drhalftone/AuV2-SLI/LauPythonCamera_Pt_Stack/mech/README.md

# Mechanical models — camera sensor, bracket, stack shroud, and the printed enclosure

| | writes | |
|---|---|---|
| `gen_sensor_step.py` | `../3dmodels/NOIP1SN1300A_LCC48.step` | the PYTHON 1300 package — the reference body everything else is designed around |
| `gen_socket_tile.py` | `../3dmodels/camera_socket_tile.step` | iteration 0 of the bracket: the contact tile |
| `gen_stack_shroud.py` | `../3dmodels/stack_shroud_<layer>.step` | **CNC aluminium** shroud rings, one per board of the Alchitry stack |
| `gen_lens_box.py` | `../3dmodels/camera_lens_box.step` | **C-mount lens box** — open-bottomed, straddles the board, gravity-seated lens. Also the **upper half** of the two-part enclosure |
| `gen_base_box.py` | `../3dmodels/camera_base_box.step` | **base box** — the lower half: encloses the Hd+/Ft+/Pt V2 and sandwiches to the lens box |
| `gen_enclosure_assembly.py` | `../3dmodels/camera_enclosure_assembly.step` | **both halves in one file** — what you open to check they meet; not a printed part |
| `gen_stack_assembly.py` | `../3dmodels/stack/*.step` | **the real boards**: camera + ESP32 card exported from KiCad, Pt V2 / Ft+ / Hd from Alchitry's STEPs, mated on the DF40 sites into `board_stack.step`, and with both case halves into `camera_stack_enclosure.step`. Needs OCP (cadquery) and kicad-cli; not a printed part |
| `gen_lens_holder.py` | `../3dmodels/camera_lens_holder.step` | M12 / S-mount alternative: plate on four posts with a threaded barrel |
| `step_writer.py` | — | shared AP214 writer and 2D helpers |
| `check_step.py` | — | validates any of the above |

Regenerate; do not hand-edit a STEP. Output is byte-reproducible, so a regenerated file
that differs is a real change.

```
python gen_sensor_step.py                    # typical dimensions
python gen_sensor_step.py --tolerance max    # worst-case envelope
python gen_socket_tile.py
python gen_lens_box.py --bosses --open-face W --pcb-t 7.1 --washer-t 2.5 --port-notch W:2.5:20.5:-0.5:2.5 --port-notch W:-8.0:7.0:-5.0:1.0   # spacer stack (d6201f5) + USB-C notches
python gen_base_box.py --open-face W         # ...and the lower half: 24.5 mm spacer stack, nut raised for M2 x 30
python gen_enclosure_assembly.py             # both halves in ONE file, to check the fit
python gen_stack_assembly.py                 # real board stack (camera/Pt/Ft+/ESP32/Hd) + both halves, ~1.5 min
python gen_lens_holder.py                    # the M12 alternative
python check_step.py
```

The **printed enclosure is those two commands** — `gen_lens_box.py` is the upper half and
`gen_base_box.py` the lower, split on the lens box skirt bottom at z = −7.10 (spacer stack). Run them in
that order: the base box reads the lens box's STEP and refuses to emit if the halves would not
meet. See [the base box](#gen_base_boxpy--the-base-box-and-the-two-part-enclosure) at the end.

The first section below covers the sensor; [the socket tile](#the-socket-tile-iteration-0)
and [the lens mounts](#the-lens-mounts) are further down.

## The lens mounts

Both read `../LauPythonCamera_Pt_Stack.kicad_pcb` on **every run** for the board outline,
the four Ø2.2 corner holes, U1's position and rotation, and every component courtyard.
Neither hard-codes board geometry, and both **fail the build** rather than warn when a
wall, post or boss would land on a part. A holder that fouls a 0402 is something you
discover with a scalpel.

The optical axis is **not** the package centre. `OPTICAL_CENTER = (-0.17924, +1.36714)`
(Table 32) puts it at KiCad **(135.821, 80.633)** with U1 at (136, 82) unrotated. Skipping
that offset decentres the image and looks perfectly plausible while doing so.

### `gen_lens_box.py` — C-mount (preferred)

An open-bottomed box. The lens is not threaded into anything: its flange shoulder rests on
the top face and gravity holds it, board flat on a table. The bore is a **thread-in** hole,
25.4 − 0.1 = **25.3 mm** (`--bore-clear -0.10`): the lens screws into the plastic and cuts its
own thread until the shoulder lands on the top face. The number came off a printed test plate
(`gen_bore_test_plate.py`, ten holes 26.0 → 24.2 mm): 25.2 threads, 25.3 is the better fit.
`--bore-clear 0.80` restores the old 26.2 mm clearance hole.

**USB-C cable notches** (`--port-notch`) are cut up from the bottom of the **west** skirt, where the stack's USB-C ports face. Positions come from Alchitry's own STEP models, placed by `gen_stack_assembly.py`:

| port | receptacle (y, z) | notch | why |
|---|---|---|---|
| Pt V2 `J2` | y 6.97..16.03, z -6.59..-2.32 | `W:2.5:20.5:-0.5:2.5` -- 18 wide, to z -0.5, R2.5 | the port is entirely behind the skirt; a 12.4 x 6.6 overmold needs y 5.3..17.7, z -7.8..-1.2 |
| Ft+ `X1` | y -4.97..3.97, z -12.50..-8.40 | `W:-8.0:7.0:-5.0:1.0` -- 15 wide, 2.1 tall, R1.0 | the base box is open here, but an overmold's top (z -7.15) passed 0.05 mm under the skirt |

The two overlap, so they are cut as ONE stepped opening. Every corner is rounded -- the top corners to each notch's R, and the convex corners where a side meets the wall bottom or the shallower notch's floor to `--notch-flare` (1.0). A prism along Z cannot carry a radius in the wall's own plane, so the rings are cut clean over the span and the wall is put back as one block extruded THROUGH its thickness (`wall_port_block_W`) with that outline. The notch stays below `--board-relief`, so the stray-light baffle above the board is untouched.

**A 1/4-20 tripod insert** sits on the **south** wall — the side nearest `J2`, the lone 80-pin
DF40 (the north edge has `J1` *and* the 50-pin `J3`). It is a 16 mm buttress running the box's
full height (table to top face, so no overhang printed either way up) with a horizontal,
**blind** Ø8.0 × 13 mm hole for a melt-in brass insert; the wall closes the bottom, so it never
opens the cavity to light. `--insert-hole/-depth` come from the insert's datasheet;
`--insert-face none` removes it.

**The hole is THREADED to the insert** (`gen_insert_quarter20.py`: 8.0 body, 1.0-high ridge 1.0 wide at the root to a 0.3 flat, 3.5 mm MEASURED pitch, right-hand, 13.0 long). The core is 8.0 line-to-line with the body, the groove is the ridge's exact negative but cut `--thread-interference` (0.15) SHALLOWER, and the hole is 13.0 deep so the insert finishes flush. It screws in tight by hand and is heated home. Verified by placing the insert model in the hole: every crest point is in plastic, no flank or core point is. The boss is built face by face (`StepFile.polyhedron`) on a grid that follows the helix, clipped flat at both ends. `--no-insert-thread` restores the plain bore. It is built with `step_writer`'s `frame=`, which lets a prism
point along any axis.

**The top face is the optical datum.** C-mount flange focal distance is 17.526 mm from the
shoulder to the image plane, so `top surface = image plane + 17.526` = **18.786 mm** above
the PCB at the default seat height (0.0 — the sensor sits flat in the Andon socket; it was
19.786 at the old 1.0 mm seat). That one surface sets focus; everything else is
clearance. Machine or print it flat and do not sand it.

**It stands on the table, not the board.** The first version put walls on the board edge
and the clearance assertion rejected it: C31, an 0805, has its courtyard 1.8 mm in from the
left edge, leaving nowhere for a wall worth printing. Straddling the PCB removes the
constraint entirely — the 56.5 × 46.5 cavity swallows the 55 × 45 board with 0.75 mm all
round, and the box touches nothing.

`--bosses` is what makes the box hold the board rather than merely cover it, and it is worth
being precise about because it is the whole load path:

| | z | |
|---|---|---|
| top face | 15.786 → 18.786 | the optical datum; the lens shoulder rests here |
| column ×4 | 1.200 → 15.786 | hangs from the top face, bored Ø4.2 for the screw head |
| washer ×4 | 0.000 → 1.200 | a flat Ø7.0 annulus **bearing down on the PCB** at its corner holes |
| walls | −1.600 → 15.786 | stand on the table and touch nothing |

So the **walls are a skirt, not a support**. The PCB is clamped between the four washers above
and a nut below, and the board therefore hangs from the box at exactly four points — the
Ø2.2 corner holes. The Ø4.2 head pocket runs all the way out through the top face so a driver
reaches each screw without lifting the box.

The washer OD is Ø7.0 and **deliberately overhangs the cavity into the wall by ~0.25 mm**. The
corner holes are only 2.5 mm in from the board edge, so a boss small enough to stay clear of
the wall cannot also carry an M2 head. The two solids union on print, and a boss tied into the
wall is stiffer than one standing alone.

> An earlier revision of this part used Ø5 columns with a Ø2.0 locating pin entering the
> board's hole, and this README described that for a while after the code had moved on. It is
> now a washer-and-through-screw. If you are reading a Ø5 pin anywhere else, that text is stale.

### The thick wall — stray light from the boards below

**Symptom: the LED array on the Pt board was lighting the sensor.** There are two paths, and
the second one is much the larger.

**Path 1 — the perimeter slot.** The cavity is the board plus `--pcb-clear` on every side,
leaving a 0.75 mm slot running the full height of the wall all the way round. The fix is not a
part added to the box, it is the box's own wall being thicker: the cavity has to be
board-plus-clearance only **where the board is**, so above the board's top face the wall steps
inboard and stays there to the top. One face with a rebate at the bottom, not a ledge hung off
the wall.

**Path 2 — the notch, which is 164 mm² of missing board.** Everything here used the board's
*bounding box* until it was checked. The real outline has a **29 × 5.5 mm notch cut into the
east edge** — the slot that makes the Pt's LEDs visible — and a wall built on the bounding box
caps 1.4 mm of it and leaves **4.1 × 26 mm wide open** straight into the optical cavity. That
was most of the light this box was trying to keep out.

**The notch plug (`--notch-drop`, default 2.0 mm).** The thick wall stops at `--board-relief`
(+0.30) because over the board it must not touch it — but over the notch there is no board, so the
wall's underside and the gap beneath it were still in the LEDs' view. `notch_plug` fills the notch
itself from z = +0.30 down to **−1.70**, below the PCB's top surface (and 0.1 mm past its bottom),
keeping `--pcb-clear` (0.75) off the board's three notch edges and running out to the cavity wall
on the east so it prints as one piece with the box. `--notch-drop 0` removes it.

So the wall's inner face now **follows the real outline**, notch included:

```
wall   3.00 thick where the board is, 5.15 thick above it
       inner face FOLLOWS THE BOARD OUTLINE (16 edges)
       cap 1.40 mm DERIVED from the perimeter
       1 of 16 edges cut back by its own neighbours:
         26.0 mm edge (13.5,-13.5)->(13.5,12.5)   0.07 mm   (R14)
       -> 99.0% of the notch is now wall, not aperture
```

**The offset is per-edge, and it has to be.** R14 and R1 (0402s, 0.60 tall) sit **0.47 mm** off
the notch's inner wall, so that one 26 mm edge can only be covered by 0.07 mm — while the far
side of the board gives the full 1.40. A single uniform figure would either foul two 0402s or
throw the overlap away everywhere else. Each edge takes what its own neighbours allow.

**The cap is derived from the perimeter, not the notch.** Left uncapped each edge takes its own
maximum — up to 5.3 mm on the north edge — which makes the wall wander, eats the aperture, and
(found the hard way) deforms it enough that a boss stops straddling the boundary and its notch
cannot be built at all. So the cap is what the true outer perimeter allows, and interior edges
are reduced from it.

**It must not touch the board.** The four washers are the seating datum; wall material coming
down proud would fight them and could rock the PCB. Hence `--board-relief`.

#### The boss notches, and the screws they nearly buried

A thick wall runs straight through the four screw-head pockets: each pocket's centre is inside
the aperture while its circle reaches past **both** edges near the corner. Cutting it as a hole
is not available — a hole crossing its own outline is not a hole, and `prism()` would emit a
solid that is not watertight rather than an error. So the aperture is **unioned with a circle
at each boss**: the pocket lies wholly in the void, and the wall stays a **connected ring** with
material outboard of every pocket. Nothing is lost optically — the washer and column are the
same diameter and fill exactly those notches.

> **This bit, twice.** The first version was analytic and rectangle-only; it ran two of the four
> arcs the long way round and produced a closed, valid, entirely plausible aperture that buried
> two screw heads in 1 mm of wall — watertight, right genus, right volume, every check in this
> repo passed. (The shelf it replaced had the same defect quietly: **3.20 mm of clear width for
> a 3.80 mm M2 head**.) `gen_lens_box.py` now walks the full head circle against the aperture at
> every boss on every run:
>
> ```
> WALL BURIES A SCREW HEAD at (-33.50, 19.50): 23 of 72 points on the 4.2 mm
> head circle fall in wall material.
> ```
>
> `union_circle()` is now general — the real outline has chamfers, so a boss can straddle three
> edges and the analytic form simply does not apply.

**Geometry stops the direct path; absorption deals with the rest.** Print this part in a
**matte black** material. `--no-thick-wall` returns the old open cavity.

### The seam joint — tongue and groove

The two halves meet at z = −1.60 in a 3.00 mm wall. That seam started as a plain butt
joint located only by the four screws, which left it both unregistered and — since the wall
is the same wall the light lip protects — a **straight-through gap into the enclosure**.

```
tongue   1.20 wide x 1.50 tall on the base box rim, z -1.80 -> -0.30
groove   1.50 wide x 1.70 deep in the lens box wall, z -1.60 -> +0.10
         clearance 0.150 mm per side, both faces
         engagement 1.300 mm, axial free play 0.400 mm
         legs 0.750 mm either side of the groove in a 3.00 mm wall
```

**The board stack is the axial datum, not the seam.** The screws clamp the stack between the
lens box's washers and the base box's bosses. If the two halves *also* met face to face there
would be a second load path and **print tolerance, not the design, would decide which one
won** — a base box 0.1 mm tall would stop the stack being clamped at all and bow both parts
instead. So the base rim stops `--seam-relief` (0.20 mm) **short** and the halves never touch,
and the groove is cut deeper than the tongue is tall so the tongue cannot bottom out either.
Same reasoning as the shroud's `--relief`, and as the lip standing off the board.

That 0.20 mm gap is not a light path, because the tongue baffles it — which is the second
reason to have the joint at all.

**The joint is defined once.** `seam_profile()` lives in `gen_lens_box.py` and
`gen_base_box.py` **imports** it, so the tongue and the groove come from the same call. Two
files computing the same joint from the same formula is exactly the arrangement that drifts
the first time one is edited, and a tongue 0.2 mm proud of its groove is invisible in either
STEP on its own.

The tongue is centred in the wall so the legs are equal, and each profile's corner radius is
the outer radius less that profile's inset — which keeps the groove concentric with the wall
and the legs a uniform 0.75 mm right around the corners. A square joint inside a rounded wall
pinches to about a third of its width at the corners.

**And it is checked against the part it mates to, not against its own parameters.**
`gen_base_box.py` reads the groove's real faces out of `camera_lens_box.step` — the hole in
`wall_seam_outer`, the outline of `wall_seam_inner` — and refuses on a measured interference,
on a tongue that would bottom out, or on a lens box built with `--no-groove`:

```
TONGUE WILL NOT ENTER: outer face has -0.050 mm of clearance against
the groove in camera_lens_box.step.

TONGUE BOTTOMS OUT: it enters 2.00 mm into a 1.70 mm groove.
The joint would then set the spacing instead of the board stack.

NO GROOVE IN THE LENS BOX. This part's tongue has nothing to enter.
```

**The joint stops where the opening starts.** The tongue was a single closed ring, so it ran
straight across the `--open-face` opening — the one cut for the HDMI and USB-C ports. That is
wrong twice over: it bars the opening, and on that side there is **no wall beneath it**, so it
is a 1.2 × 1.5 mm rail bridging the full width of the gap in mid-air. It would print as a
sagging bridge holding nothing up. The tongue is now built as bars on the same split as the
walls and skips open faces (and any window that reaches the rim):

```
tongue   1.20 wide x 1.50 tall on the rim, z -1.80 -> -0.30, in 3 segment(s)
         NO tongue on face(s) E
```

The lens box takes the **same** `--open-face` and fills its groove back to solid over exactly
that span, so no empty channel is left along the bottom of the wall above the access slot. Its
*wall* is never opened — that half is the optical enclosure.

> **The two halves are told separately, so they can disagree.** Give `--open-face E` to the base
> box only and the lens box keeps a harmless empty groove. Give it to the **lens box only** and
> its fill sits exactly where the tongue still is — a solid interference a millimetre wide,
> invisible in either file alone, that would simply stop the halves closing. `gen_base_box.py`
> reads the fills out of `camera_lens_box.step` and refuses:
>
> ```
> SEAM CLASH: wall_seam_fill_E in camera_lens_box.step fills the groove over
> x 20.50..22.00 y -24.50..23.50, but tongue_E_0 still has tongue there.
> ```
>
> `gen_enclosure_assembly.py` passes the same faces to both, so the assembly cannot drift.

> Splitting the wall for the groove also split the solid named `walls` into three.
> `gen_base_box.py`'s `upper_half()` now reads **every** solid named `wall*`; matching only
> `walls` would have read the mating face as the *top* of the groove and shifted the whole
> lower half by the groove depth.

### `gen_lens_holder.py` — M12 / S-mount

Kept as the alternative. A plate on four corner posts with a tapped barrel; bore 11.5 mm is
the tap drill for M12 × 0.5. Note the PYTHON 1300's image circle is 7.87 mm diagonal — a
**1/2″ format** — and many M12 lenses are only corrected for 1/3″ and will vignette.

### The number that is not published

`--seat-z`, the sensor's seating plane above the PCB, defaults to **0.0 mm**: since 2026-10 the
colour sensor sits flat on the PCB in the Andon socket (it was 1.0 mm for the earlier mono build —
`--seat-z 1.0` regenerates those parts, plus `--plate-z 4.5` for the M12 holder). It is not in any
datasheet — `gen_socket_tile.py` says so outright — and it shifts the top face, and
therefore **focus**, 1:1. Measure the glass height with calipers before committing to a
machined part. A C-mount lens at f/1.4 has very little depth of focus.

Every dimension comes from `docs/datasheets/NOIP1SN1300A.pdf` — **Table 31** (Mechanical
Specification), **Figure 50** (Package Drawing), **Table 32 / Figures 51–52** (Optical
Center) and **Table 33** (tray thickness, used only as a cross-check). Nothing is scaled
off a drawing or recalled from memory.

## Coordinate frame

Origin at the centre of the package footprint, on the **seating plane** (package bottom);
+Z out through the glass. X and Y are the datasheet **top view** of Figure 52 — pin 1 at
the middle of the left edge, numbering counter-clockwise. That is the same view as the
KiCad canvas for U1.

`gen_sensor_step.py` asserts its pin ring against U1's socket footprint in the
`.kicad_pcb` on every run, including the left-edge handedness test from README §12
(`43,44,45,46,47,48,1,2,3,4,5,6`, top to bottom). The footprint was mirrored once already;
a mirrored model here would be the same class of expensive mistake, and it would look
perfectly correct.

## Datums

| | min | **typ** | max |
|---|---|---|---|
| Body, square | 14.09 | **14.22** | 14.42 |
| Overall height, seating plane → top of glass | 1.820 | **2.250** | 2.710 |
| **Image plane**, seating plane → top of die surface | 1.165 | **1.260** | 1.405 |
| Top of glass → image plane | 0.655 | **0.990** | 1.305 |
| Glass lid thickness (13.60 sq) | 0.5 | **0.55** | 0.6 |

**Optical axis: x = −0.179 mm, y = +1.367 mm from the package centre.** Active area
6.1440 × 4.9152 mm (1280 × 1024 at 4.8 µm). **Centre the lens on the optical axis, not on
the package and not on the socket** — the Y offset is 1.37 mm, far too large to ignore.

## What this means for the bracket

**The height tolerance is 0.89 mm.** Overall height runs 1.820–2.710 mm and the image
plane itself runs 1.165–1.405 mm. Nothing that references the top of the glass can be
rigid, and focus has to be adjustable — a fixed-height lens standoff cannot work across
the band.

**Press on the ceramic rim, never on the glass.** The nominal ledge between the 14.22 mm
body and the 13.60 mm lid is only 0.31 mm per side, and Figure 50 annotates a "Max Glass
Overlap" of 0.5, which reads as the lid being allowed to sit off-centre. Treat the ledge
as neither symmetric nor guaranteed until measured on a real part.

**The bracket is the retention.** The Andon 680-48-SM is open-frame — no lid, no clamshell,
no clip — and holds the sensor by contact friction alone (README §7). Anything handled or
vibrated needs the bracket to hold the sensor down.

**Clear the socket, not just the sensor.** Socket body 16.764 mm square, 2.90 mm tall, with
solder pads reaching ±11.176 mm from centre. Pass `--socket-seat MM` to include it as a
keep-out solid.

### The one number that is missing

**The height of the sensor's seating plane above the PCB is not documented** — not in the
datasheet, not in the Andon catalog. Everything in this model is referenced to the seating
plane, so that single measurement is what places the optical axis in board coordinates.
Measure it on the assembled board with calipers or a depth gauge and pass it as
`--socket-seat`. Until then the model is correct in its own frame and unplaced in the
board's.

## Modelling choices

- The ceramic is a **solid envelope** with no cavity — the cavity is not dimensioned
  anywhere in the datasheet. The glue line under the lid is rolled into the ceramic, which
  gives the same outer envelope in one fewer body. Derived typical height is 2.250 mm
  against Table 33's 2.28 mm, which includes glue.
- `die_REF` and `active_area_REF` are **reference geometry** and interpenetrate the
  ceramic. `active_area_REF`'s **top face lies exactly on the image plane**. Hide them, or
  drop them with `--no-reference`.
- Castellations are modelled as 0.51 mm square notches 0.19 mm deep (Figure 50 gives
  0.51 ±0.05 width and R0.19). They only remove material, so the envelope is exactly
  14.22 mm either way; `--no-castellations` gives a plain rounded square.
- Corner radius R0.20, faceted in 4 segments.
- The header timestamp is fixed, so regenerating produces a byte-identical file.

## The socket tile

A square frame that sits **flush on the PCB**, with a window the sensor sits in, 48 wire
slots on the sensor's pin pitch, and two legs through the board's index holes.

**This is the socket-less build.** Sitting flush means the Andon socket is not fitted —
the tile's window at ±7.400 is inside the socket body at ±8.382, so the two cannot both be
there. That is not a compromise, it is the point: if the socket were fitted it would make
the connections itself and there would be nothing to wire. Here the sensor sits directly on
the board and 48 hand-soldered wires do the socket's job, with the tile holding the sensor
in place and guiding each wire to its pad.

> **Check this is still the plan.** This part was drawn when the socket looked unobtainable.
> As of 2026-08-07 it is not — Andon builds it to order in **6–8 weeks**, comfortably inside
> the sensor's ~27-week lead, so the socket is off the critical path (board README §15.1).
> Hand-soldering 48 nets is a lot of work to take on for a problem that turned out to be
> smaller than it looked. The tile stays worth having as a fallback, and `--standoff 2.9`
> returns the socketed geometry — but decide deliberately rather than by inertia.

**Both models now share one origin.** With the sensor sitting directly on the board, its
seating plane *is* the PCB top surface, so `gen_sensor_step.py`'s z = 0 and this file's
z = 0 are the same plane. Open the two STEPs together and they land correctly in all three
axes. (The unmeasured socket seating height above only matters for a socketed build.)

| | default | |
|---|---|---|
| Outer | **20.352 mm** square, R0.8 | derived: pads end at 11.176, less `--expose 1.0` |
| Window | 14.80 mm square, R0.4 | 0.19 mm/side over the sensor's worst-case 14.42 body |
| Thickness | 1.50 mm | |
| Underside | **z = 0** | flush on the board |
| Locating legs | 2 × Ø1.40, **1.70 mm tall** | through the 1.6 mm board, 0.10 proud beneath |
| Wire slots | 48 × 0.51 wide | on the sensor's own 1.016 mm pitch |

**The outer size is derived, not chosen.** `--expose` says how much of each solder joint to
leave visible past the tile edge; the pads run 8.636 → 11.176 from centre, so the default
1.0 mm puts the edge at 10.176. Change `--expose` and the tile follows. `--outer` overrides
it if you want a flat number.

Note the trade-off that buys: the tile no longer shields the whole contact ring. It covers
8.636 → 10.176 of each 2.54 mm pad and deliberately leaves the last millimetre open so an
iron can reach it.

Every one of those is a first guess a test print will move — they are all flags.

### The wire slots

Each slot runs the full height of the window wall as a 0.40 mm deep groove, then turns onto
the bottom face and runs out through the rim as a 0.40 mm deep channel. Slot positions come
from `gen_sensor_step.pin_ring()` rather than being re-derived, so they line up with the
sensor's castellations by construction and inherit that ring's cross-check against U1's
footprint.

**The board's pads sit on that same pitch, at the same along-edge offsets — to 0.000000 mm.**
So a wire leaving sensor pin N and running straight out lands on pad N, with no crossing and
no fan-out: a 1.526 mm run from the sensor edge at 7.110 to where the pads start at 8.636.
That is what makes a straight radial channel the right shape rather than a convenient one,
and the generator asserts it against the board every run.

The turn is why the tile is **two stacked solids**, `tile_upper` and `tile_lower`, split at
z = 0.40. A prism has vertical walls and cannot change profile with height; stacking two is
what lets the groove change direction. Union them to print.

Three things about the slots worth knowing before printing:

- **The ribs between slots are 0.506 mm** — 1.016 pitch less 0.51 slot. That is at or under
  a single FDM extrusion. Print this on a resin machine, or slot every second pin to get
  1.52 mm of pitch. The generator warns about it.
- **The channels run through the rim**, so a wire exits at the tile edge and lands on the
  exposed millimetre of pad. `--channel-reach` stops them short if you want a rim instead.
- **Breaking through severs the bottom layer into 48 pieces** — eleven between the slots on
  each side, plus one wrapping each corner. That is the geometry, not a modelling
  compromise: each piece hangs from the upper ring, which is what holds the tile together.
  They are separate solids (`tile_lower_01` … `48`); union everything to print.
- **The corner is a square step, not a radius.** Give the wire its own bend relief.
- **The exit is flat.** With the tile flush, the channel floor *is* the board, so a wire
  runs level from the castellation onto its pad with no bend at the rim. (Raise
  `--standoff` and that stops being true; the generator reports the resulting bend angle.)

`--no-slots` gives the plain tile back.

The generator re-derives the index holes, the socket body rectangle and the pad reach from
the `.kicad_pcb` on each run and fails if any has moved, so the tile cannot silently drift
away from the board it mounts to.

**The tile clears everything on the board.** Ten footprints fall under it, all on the
bottom layer — the U1 decoupling caps moved to the underside per README §14. Nothing on
the top layer is in the way, which is what makes flush mounting possible at all.

**What it does not do: retain the sensor.** The tile surrounds the sensor without covering
it, so nothing holds the part down vertically. That wants a separate lid, and it is the
obvious next iteration.

### The legs

Ø1.40 in the Ø1.60 index holes — 0.20 mm of diametral clearance — running 1.70 mm from the
tile's underside, so they pass through the 1.6 mm board and stand 0.10 mm proud beneath it.
Nothing on the bottom layer is near either leg; the ten underside caps are all elsewhere.

`--pin-engage` sets the depth. Shorten it below 1.6 and they stop inside the board, which
the generator reports rather than leaves for you to notice.

**The socket interference that blocked the earlier iterations is gone**, and worth recording
why. Both index holes sit exactly on the socket body outline — one at x = −8.382, one at
y = +8.382, against a body of ±8.382 — so any post centred in either had half its section
inside the socket's footprint. The holes are there to take the Andon part's **own** index
pins, so they were under its body by construction. With no socket fitted, they are simply
empty, and the legs use them as intended. If you go back to a socketed build
(`--standoff 2.9`), the interference returns and the generator says so again.

`--pin-length` shortens the leg itself and turns the remainder into a `--boss-dia`
shoulder. That mattered when the tile stood 2.90 mm off the board and the post would
otherwise have been a 4.1 mm needle. Flush, the leg is 1.70 mm and needs no shoulder.

## STL, for tools that will not read STEP

`--stl` writes a binary STL alongside the STEP. **These models are already polyhedra**, so
the STL is exact — nothing is tessellated or approximated on the way out, and the mesh
volume matches the B-rep solid to the last decimal.

```
python gen_socket_tile.py --stl
python gen_sensor_step.py --stl --no-reference
```

STL carries no units; everything here is **millimetres**, so say so on import.

Committed STLs: `camera_socket_tile.stl` (2232 triangles) and `NOIP1SN1300A_LCC48.stl`
(856 triangles, built with `--no-reference`).

Caps are triangulated by ear clipping, not a fan from vertex 0 — neither the sensor
outline nor the tile's cap is remotely convex. Caps with a hole are first merged into one
simple polygon by the standard keyhole bridge.

**SketchUp** cannot import STEP without a paid extension, and it discards geometry below
about 0.001 inch — which is why the sensor STL is generated without reference geometry.
The `active_area_REF` plate is 0.02 mm thick and would not survive; the generator warns
when any solid is under 0.1 mm. The optical axis is in the datums table above if you need
to place it by hand.

The tile's STL contains the plate and both pins as **separate shells**. That is what a
slicer expects and will union, but union them explicitly if you are modelling with it.

## Validation

`check_step.py` re-reads the STEP independently of the code that wrote it and checks that
every edge is used exactly twice per solid (once in each direction), that V − E + F = 2,
that each face loop winds counter-clockwise about the outward normal its plane declares,
that every inner bound winds opposite its outer loop (which is what makes a window a hole
rather than a second region), and that the enclosed volume integrated over the faces
matches the volume computed analytically from the design dimensions. The volume test is
the one that catches an inside-out solid, which every purely topological check passes.

STL export applies the same two tests to the triangles before writing — every half-edge
matched exactly once, positive enclosed volume — because a triangulation bug in a
non-convex cap would otherwise stay invisible until it printed. It checks **per solid**,
not across the model: stacked solids share edges on their common plane quite legitimately,
and checking globally rejects them. (It did, the first time the tile grew slots. The check
was wrong, not the geometry — but it was the check finding the disagreement that made that
worth looking at.)

It reports **genus** rather than asserting a fixed Euler characteristic — the sensor's
bodies are genus 0, the tile is genus 1 because the window goes all the way through.

Both models were additionally imported with OCCT (`cadquery`), which reports every solid
valid with volumes and bounding boxes matching the tables above. `check_step.py` needs no
third-party packages; the OCCT pass was a one-off confirmation.

---

## `gen_stack_shroud.py` — the stack shroud (CNC aluminium)

One rectangular ring per board — Hd+ / Ft+ / Pt V2 / camera — surrounding the PCB
and the gap above it, so the rings stack beside the boards to form a tube.

**Outboard of the PCB, not between the boards.** The measured board-to-board gap is
3.68 mm and it is already full of components and connectors; there is nothing to fit
into. The rings clear the 55 x 45 outline laterally instead.

### Two schemes, and it refuses to blur them

Four rigid aluminium rings totalling 0.2 mm over will pry the stack apart, and the
only thing holding it together is a row of 0.4 mm-pitch DF40 connectors. Aluminium
does not yield the way a printed part does — the connector will.

- `--scheme shroud` (default): rings cut SHORT, touching nothing. The generator
  asserts the total is under the board stack and exits otherwise.
- `--scheme spacer`: rings machined to the pitch exactly, corner bolts carrying the
  load. Refuses to emit without `--i-verified-hole-align`, because it needs aligned
  corner holes on all four boards and nothing in this repo verifies that.

### Aluminium is conductive — a design input, not a footnote

Clearance is 0.75 mm per side, not the 0.3 mm that would do in plastic, because
board edges carry ground pours and via stubs. Every ring has a bond tap so the
shroud is **deliberately grounded**: a floating metal box beside 720 Mbps LVDS and
the FT601's source-synchronous bus is a coupling path. Bonded, it is a shield.
Anodising is not the insulator.

### Cutouts require a cited source

`--notch` will not work without `--notch-source`, which is stamped into the STEP
description. There is **no Alchitry board CAD in this repo**, so connector positions
for the Hd+/Ft+/Pt V2 are unknown — and a STEP file looks authoritative in a way a
caveat in conversation does not. A shop cannot tell a measured cutout from a guessed
one. **The committed rings are closed bands**: no cable can leave the stack, on
purpose, until real positions are measured.

---

## `gen_base_box.py` — the base box, and the two-part enclosure

The enclosure is **two half boxes sharing one split plane**, not a new design:

```
  +18.786  ---- top face = OPTICAL DATUM ---------.
                                                  |  camera_lens_box.step
   -1.600  ==== MATING PLANE ===================== :  (unchanged)
                                                  |
                [ camera PCB ]  above the split    |  camera_base_box.step
                [ Pt V2 ]                          |
                [ Ft+ ]                            |
  -19.000  ---- Hd+ bottom face                    |
  -21.000  ---- floor top, four support bosses     |
  -24.000  ---- floor bottom, four nut pockets ----'
```

`gen_lens_box.py` already stopped its walls at **z = −1.60**, the camera PCB's bottom face, so
the lens box *is* the upper half with no change at all. The base box picks up exactly there.

```
python gen_base_box.py --open-face E          # buildable today, no measurements needed
```

### The HDMI and USB-C openings — measured from Alchitry's own CAD

```
python gen_base_box.py --open-face E --alchitry-ports
```

Positions come from the **official** Alchitry models, not from guesswork:

```
https://cdn.alchitry.com/docs/Hd-V2/Hd.step       45.6 MB   MICRO-HDMI x2
https://cdn.alchitry.com/docs/Ft-V2/FtPlus.step   65.3 MB   USB-C-MOLEX
```

Neither is committed — that is 110 MB of vendor CAD. The *result* of reading them lives in
`ALCHITRY_PORTS` at the top of `gen_base_box.py`, so the enclosure rebuilds without them.
(`Br.step` at the same CDN path is byte-identical in size to the copy already on this machine,
which is how the source was confirmed.) **There is no Pt V2 model** — five plausible CDN paths
all 403'd; Au and Br are there, Pt is not. That is fine here: the Pt is programmed before the
stack goes in the box.

**Tying the frames together is the part that could silently be wrong.** All three boards carry
the same DF40 sites, so the sites are the datum:

| | 50-pin | 80-pin | 80-pin |
|---|---|---|---|
| Hd / Ft+ | (16.5, 41.0) | (38.0, 4.0) | (38.0, 41.0) |
| camera board plugs | (16.5, 41.0) | (38.0, 4.0) | (38.0, 41.0) |

They match to 0.00 mm — but only once KiCad's **Y-down** is converted to the STEP frame's
**Y-up**, giving `model_x = alchitry_x − 36`, `model_y = alchitry_y − 23`. Read carelessly the
same numbers look like a *mirrored* stack, and that reading also "works" arithmetically — it
just puts every port on the wrong face. The DF40 check is what settles it.

**What was measured, and where it put the ports:**

| board | part | alchitry | model |
|---|---|---|---|
| Hd | MICRO-HDMI #1 | ay 10.00…15.00 @ ax −0.54…4.00 | y −13.00…−8.00 |
| Hd | MICRO-HDMI #2 | ay 22.50…27.50 @ ax −0.54…4.00 | y −0.50…4.50 |
| Ft+ | USB-C-MOLEX | placed (4.50, 22.50) | (−31.50, −0.50) |

All three are on the `ax ≈ 0` edge — the **WEST** face. The east opening is the LED window
(the camera PCB's notch at ax 49.5…55); the two are opposite ends of the board and always were.

**The openings are sized for a CABLE, not a connector, and that part is not from CAD.** A
plug's overmold is not on the board, so it is not in any board model. The along-edge span and
the height come from typical micro-HDMI (Type D) and USB-C overmolds, ~12 × 7 mm, centred on
the measured port centres — and that distinction is stamped into the STEP description rather
than left to be inferred.

**The two HDMI ports share one slot.** Their centres are 12.50 mm apart and an overmold is
about 12 mm wide, so two windows would merge anyway — and two cables cannot sit side by side at
that pitch regardless. One slot spanning both is the honest shape.

Heights are *derived*, not guessed: each connector stands on its own board's top face, and the
board faces follow from the measured 19.00 mm stack. Only how that stack divides is assumed
(`--board-t`, 1.60 mm), which is the same caveat the reference plates carry.

> The wall keeps a solid band from z −6.50 to −1.80 across the full width, so the seam tongue
> is still supported above both openings.

### It refuses to emit a box no cable can leave

Every external connector in the design — HDMI, USB 3, power, JTAG — is on one of the three
boards **this** half encloses. So a sealed base box is not a conservative default, it is a
useless part, and the generator will not produce one silently. Pass `--open-face N|S|E|W` to
leave a whole wall off (needs no measurements at all), `--window edge:along:width:zbot:ztop`
with a `--window-source` for a measured cutout, or `--closed-box` if you really do want it
sealed. Window `zbot`/`ztop` are measured **up from the Hd+ bottom face** — a surface you can
rest calipers on — not as signed offsets from a datum buried inside the sensor.

`--window-source` is stamped into the STEP description, for the same reason
`gen_stack_shroud.py` requires `--notch-source`: a shop, or you in six weeks, cannot tell a
measured cutout from an invented one by looking at the file.

### The mating surface is checked against the part it mates to

The base box does not assume the lens box's dimensions. It **reads `camera_lens_box.step` on
every run**, pulls the `walls` solid, and asserts its own outer profile and top face match —
outer x0/x1/y0/y1 and the mating plane, to 1 µm. Regenerate the lens box with a different
`--wall` or `--pcb-clear` and this part fails loudly instead of printing a base that overhangs
by 1.5 mm. Two halves that do not meet is exactly the failure a STEP file hides until it has
been printed.

### The stack is captured, never hung

Four **M2 × 25** socket caps go in from the **top**, through the lens box's driver pockets,
down the whole board stack, into nuts captured under this floor:

```
screw head → lens box washer → camera PCB → (stack in compression, connector
bodies bearing) → Hd+ → support boss → floor → nut
```

That matters. Lengthening the lens box's walls alone would leave the camera board as the only
clamped board, with the Pt V2, Ft+ and Hd+ hanging beneath it **on the DF40s alone** — 19 mm of
board stack carried by three 0.4 mm-pitch connector pairs, in tension, the moment the assembly
is picked up. `gen_stack_shroud.py` was written to avoid precisely that; this arrives at it
from the other direction. Captured between the washers above and the four bosses below, neither
connector pair ever sees tension.

`--floor-clear` (default 2.0 mm) is the gap under the Hd+ for its bottom-side parts; the four
Ø7.0 bosses bridge it at the corner holes and are the only thing the stack rests on.

### The stack height is measured, not derived

**19.00 mm, camera PCB top surface → Hd+ bottom surface**, measured on the assembled stack and
passed in directly. It is *not* rebuilt from board thickness × gap, because that product is
what was wrong before:

| | |
|---|---|
| `gen_stack_shroud.py` computes | 17.44 mm — 4 × 1.60 mm boards + 3 × **3.68** mm gaps |
| measured | **19.00 mm** → implies a **4.20** mm gap |
| Br.step fits `DF40HC(4.0)` sockets | 4.0 mm nominal stacking height |

4.20 is close to the connector's own 4.0 nominal; 3.68 is not. **Treat the 3.68 mm in
`gen_stack_shroud.py` as suspect** — it is not used here, and the shroud's ring heights and its
"rings are 1.00 mm short" safety margin are both derived from it.

### What is still unverified

The four screws must pass the corner holes of the **Hd+, Ft+ and Pt V2**. The Ø2.2 pattern at
(2.5, 2.5) / (2.5, 42.5) / (52.5, 2.5) / (52.5, 42.5) is confirmed on the camera board (its own
KiCad) and on the Br (`Br.step`, four r=1.1 cylinders at exactly those centres) — but there is
no CAD for those three anywhere in this repo. An M2 in a Ø2.2 hole has 0.2 mm to spare. If a
board differs the screw simply will not pass, which you discover at assembly with nothing
damaged, so the generator warns rather than refuses.

---

## `gen_enclosure_assembly.py` — both halves in one file

The two half boxes print separately. This is the file you **open** to check they meet.

```
python gen_enclosure_assembly.py                 # 23 solids, 43.79 mm tall
python gen_enclosure_assembly.py --no-reference  # printed parts only
```

**It does not re-describe any geometry.** It runs the two generators, captures the `StepFile`
each one built, and replays their recorded prisms into a single file — so every solid is the
same geometry as the part you print. Verified by comparing all 19 solid volumes against the
half files: every one matches to better than 1e-9 mm³. If this file and the halves ever
disagree, that is a bug in the assembler, not a difference in the design.

**The board plates are reference geometry and half assumed.** Two numbers about the stack are
known — the 55 × 45 outline (from KiCad) and the **measured 19.00 mm** camera-PCB-top to
Hd+-bottom. Board thickness is *not* measured; 1.60 mm is assumed, which then forces the
pitch:

```
pitch = (19.00 - 1.60) / 3 = 5.800 mm     gap = 4.200 mm
```

The two **outer** faces are measured and correct. The two **intermediate** boards sit where
that assumption puts them — check clearance against them, do not dimension from them. They are
named `board_REF_*`, coloured green so they cannot be mistaken for a printed part, and
excluded from the STL. `--no-reference` drops them.

Contact is by design, not coincidence: the lens box's washers meet the camera plate at z = 0,
and the base box's bosses meet the Hd+ plate at z = −19.00.

---

## A measured fault on this machine: silently corrupted STEP writes

While generating the base box, the same command run 20 times produced a file that differed
from the other runs **4 times**. Every instance had the same shape:

```
good  #4256=CARTESIAN_POINT('',(-32.6514719,-19.6514719,-22.));
bad   #4256=CARTESIAN_POINT('',(-32.6511719,-19.6514719,-22.));
                                       ^ one ASCII digit
```

One digit substituted inside the X coordinate of one point, **file length unchanged**, every
other byte identical. It is not a random bit flip: two independent runs produced the *same*
defect at the *same* line, and every instance landed in a `CARTESIAN_POINT` X value at byte
32–33 of its line. Reads are stable — the corrupt file stays corrupt when re-read — so the
damage is on disk, not in the reader.

**Why nothing in this repo caught it.** Displacing one vertex by 0.3 µm leaves a solid that is
still watertight, still has every edge used exactly twice, still has the right genus, and whose
integrated volume moves far less than `check_step.validate`'s tolerance. It passes every test
here. That is the same failure mode as the FT601 build that streamed at full rate while
corrupting half the bus: correct by every measurement being taken, and wrong.

**What was done about it.** `step_writer.write_verified()` writes, `fsync`s, reads the file back
and rewrites until the bytes match, failing loudly if it cannot. That took the rate from 4/20 to
1/25 — but note the in-process read-back **never fired** on the survivor, so that last case is
corruption occurring after the writing process has already verified and exited. This is a
system-level fault (storage, memory, or something else touching files in this tree), not a
Python one, and it is worth running Windows Memory Diagnostic and checking for an antivirus or
sync client with its hands on `Developer/`.

**It is not confined to STEP files.** Within the same session, and after the write-verify was
already in place, this tree also produced:

- a **segmentation fault** in CPython while running `gen_enclosure_assembly.py`;
- a **corrupt object in the git repository itself** — `git status` and `git fsck` both failing
  with `inflate: data stream error (incorrect data check)` on the loose object holding
  `camera_base_box.step`.

That object was recoverable only because these files are byte-reproducible: the working copy
re-hashed to exactly the corrupt object's SHA, so deleting the unreadable object and
re-running `git hash-object -w` restored the repository bit-for-bit, and `git fsck` came back
clean. Had it been a hand-edited file, the content would simply have been gone.

**Three independent symptoms — silent single-byte file corruption, a CPython segfault, and a
corrupt git object — is the signature of failing memory, not of a bug in this repo.** Treat
build artifacts produced here as suspect until the machine is cleared: run Windows Memory
Diagnostic (or memtest86), and `git fsck` before trusting a push.

**The real backstop is byte-reproducibility.** Every generator here emits a byte-identical file
for identical inputs, which is what turned an invisible one-digit defect into a one-line
`git diff`. That is why "regenerate; do not hand-edit a STEP" at the top of this file is
load-bearing and not merely tidiness — and why it is worth running `git status` after
regenerating and re-running the generator if anything you did not change has moved.

> `gen_base_box.py` uses `write_verified()`. The older generators still use a plain `open().write()`
> and should be migrated.
