drhalftone/AuV2-SLI/LauCameraTrigger_Alchitry_Stack/production/drc_report.txt

** Drc report for LauCameraTrigger_Alchitry_Stack.kicad_pcb **
** Created on 2026-06-29T13:08:04 **
** Report includes: Errors **

** Found 0 DRC violations **

** Found 0 unconnected pads **

** Found 0 Footprint errors **

** Ignored checks **
    - Footprint has no courtyard defined
    - Track endpoint not centered on via
    - Tuning profile track geometries
    - Footprint doesn't match symbol's footprint filters
    - Footprint component type doesn't match footprint pads

** End of Report **
