drhalftone/AuV2-SLI/POLARFIRE_PORT_FEASIBILITY.md

# Porting AuV2-SLI to a Microchip PolarFire Video & Imaging Kit

**Question:** Can the Alchitry Au V2 (Artix-7) SLI design be moved to a Microchip
**PolarFire FPGA Video and Imaging Kit** (`MPF300-VIDEO-KIT`, device
`MPF300T-1FCG1152I`) to do **4K60 dual-HDMI passthrough/generation**, ingest a
camera over **MIPI CSI-2** to synchronize projection and capture for structured
light illumination (SLI), and **process pixels on-chip so the FPGA outputs only
phase video**?

**Short answer:** Yes to everything — but it is a *re-architecture*, not a port.
The kit is almost purpose-built for this. The ~35% of the Au code that touches the
HDMI PHY and clocking is the hard, FPGA-specific part, and on PolarFire you do not
port it — you *replace* it with Microchip's licensed video IP. The other ~60–65%
(the actual SLI value) carries over in spirit.

---

## 1. Does the kit physically do what we want?

| Requirement | PolarFire Video Kit | Verdict |
|---|---|---|
| Dual HDMI, 4K60 passthrough/generate | HDMI 2.0 (up to **4K60**) via 12.7 Gbps transceivers; Microchip ships production HDMI **RX** and **TX** IP (1.4/2.0/2.1) plus an HDMI **loopback** app note (AN4768) — literally passthrough | ✅ Supported |
| MIPI CSI-2 camera for SLI sync | Ships with a dual-camera daughtercard (2× Sony **IMX334**, 4-lane MIPI each, up to 1782 Mbps); Microchip provides MIPI CSI-2 **RX/TX** IP | ✅ Supported |
| Process pixels on-FPGA, output only phase video | MPF300T = 300K LE + ~924 DSP blocks + **4× 4 Gb DDR4** for frame buffering | ✅ Feasible (largest effort — see §5) |

The hardware is **not** the bottleneck. The MPF300T has the transceivers for 4K60
HDMI and the DDR4 bandwidth + DSP for the on-chip math.
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
