drhalftone/AuV2-SLI/CAMERA_RTL_REVIEW.md

# PYTHON 1300 Receiver Chain — Fresh-Eyes RTL Review

Conclusions from an independent, adversarial review of the camera RTL, written into the repo
so they aren't lost in chat. Two passes:

1. **Phase 2 integration diff** (commit `3dad19d`) — 4 reviewers over the clocking rewire,
   the boot/SPI arbitration, `cam_line_buf`, and the build/XDC.
2. **The pre-existing receiver chain** — 4 reviewers, one per module (`cam_lvds_rx`,
   `cam_align`, `cam_sync_decode`, `cam_spi_master`).
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
