drhalftone/AuV2-SLI/press/stack_connector_edge.jpg

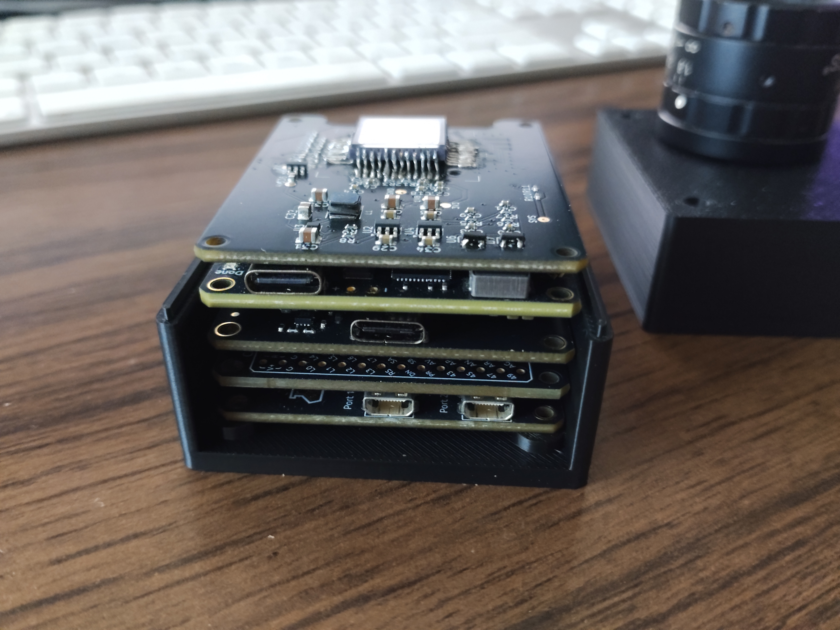
press/stack_connector_edge.jpg
