drhalftone/AuV2-SLI/press/stack_with_lens_cap.jpg

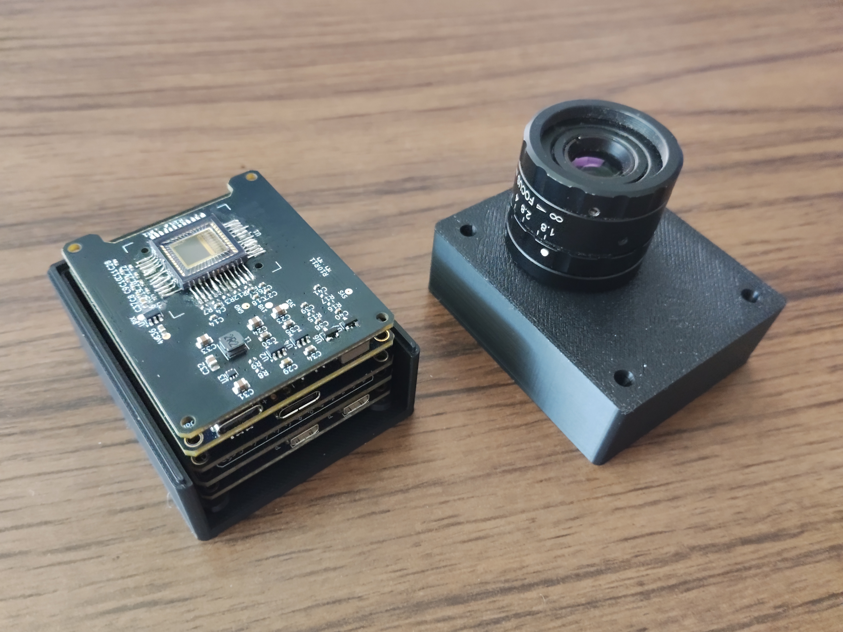
press/stack_with_lens_cap.jpg
