drhalftone/AuV2-SLI/LauPythonCamera_Pt_Stack/3dmodels/stack_shroud_camera.step

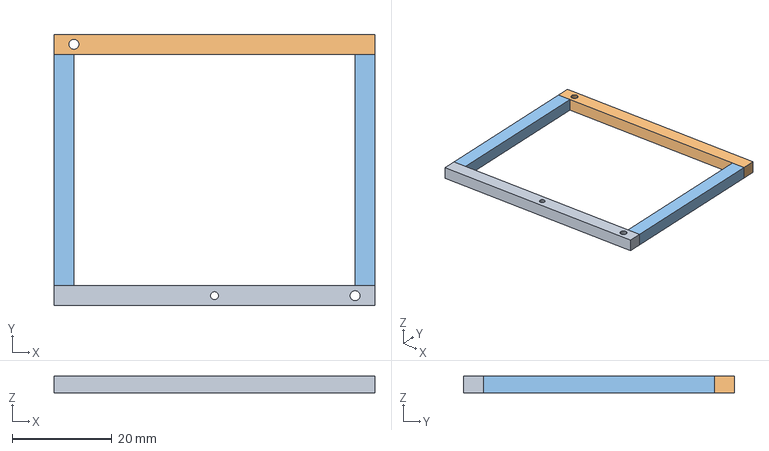
[picture p18: CAD file, 2026-08-24]
LauPythonCamera_Pt_Stack/3dmodels/stack_shroud_camera.step
64.5 x 54.5 x 3.35 mm
