drhalftone/AuV2-SLI/LauPythonCamera_Pt_Stack/3dmodels/PYTHON1300_NOIP1SN1300A_LCC48.step

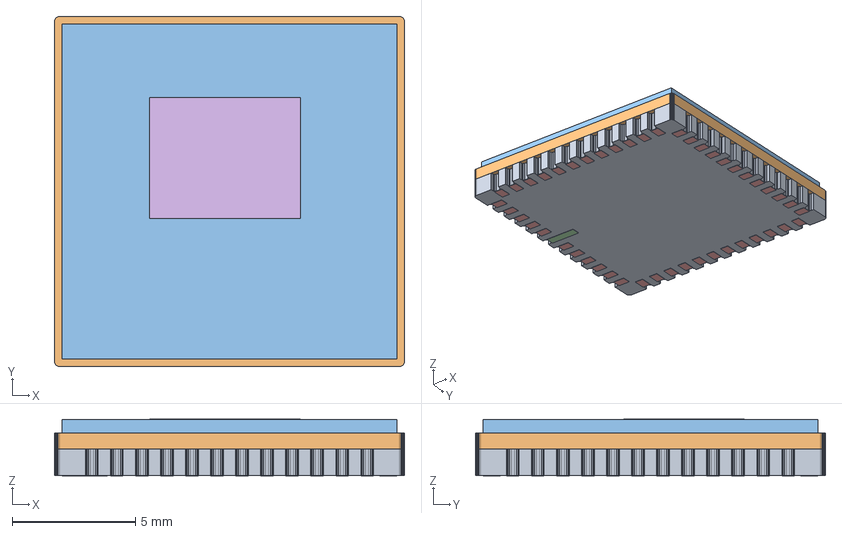
[picture p19: CAD file, 2026-08-18]
LauPythonCamera_Pt_Stack/3dmodels/PYTHON1300_NOIP1SN1300A_LCC48.step
14.2 x 14.2 x 2.31 mm
