drhalftone/AuV2-SLI/LauPythonCamera_Pt_Stack/3dmodels/camera_socket_tile.step

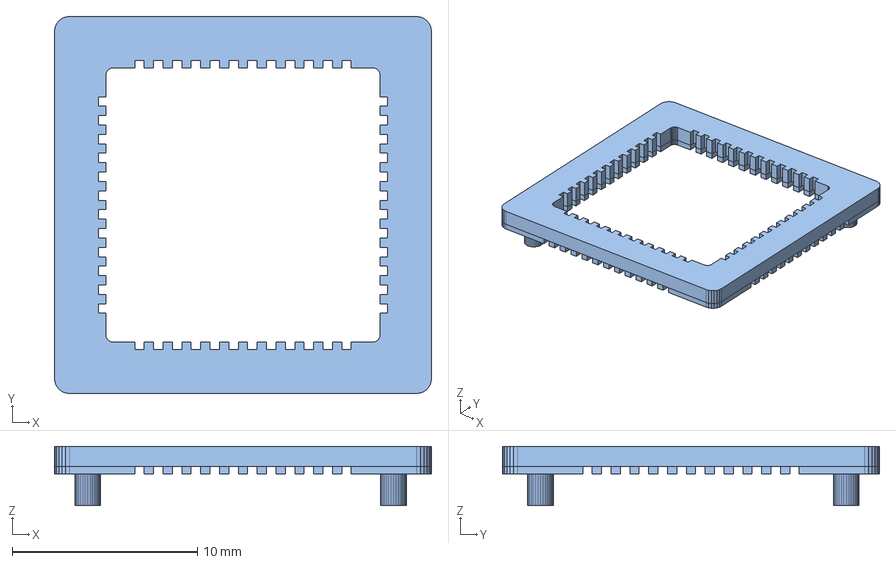
[picture p20: CAD file, 2026-08-08]
LauPythonCamera_Pt_Stack/3dmodels/camera_socket_tile.step
20.4 x 20.4 x 3.20 mm
