drhalftone/AuV2-SLI/LauPythonCamera_Pt_Stack/3dmodels/NOIP1SN1300A_LCC48.step

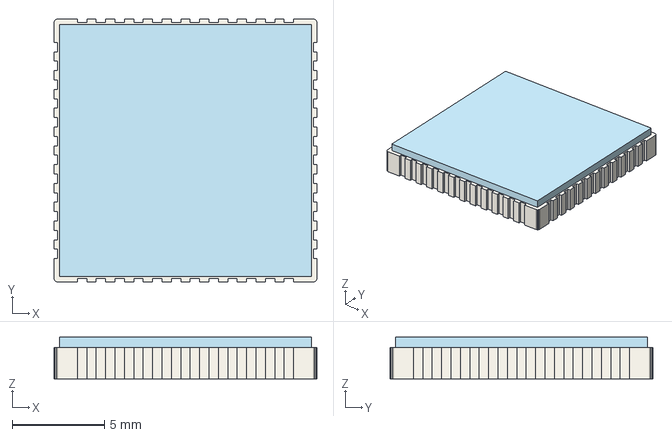
[picture p21: CAD file, 2026-08-07]
LauPythonCamera_Pt_Stack/3dmodels/NOIP1SN1300A_LCC48.step
14.2 x 14.2 x 2.25 mm
