drhalftone/AuV2-SLI/docs/machine/intel_cpu_warranty_2026-10/math_capped_5000/brandstring_1_Results.txt

CPU Brand String Test
Module Version: 1.1.0.64b.W
Start Time: Wed Oct  7 17:21:57 2026
Test Result - PASS 
Expected: Intel(R) Core(TM) 
Detected: Intel(R) Core(TM) i9-14900KF
Intel(R) Core(TM) processor detected..!!..
End Time: Wed Oct  7 17:21:57 2026
Total Time: in seconds: 0
