drhalftone/AuV2-SLI/docs/machine/intel_cpu_warranty_2026-10/math_capped_5000/TESTRESULTS.TXT

--- IPDT64 - Revision: 4.5.0.0
--- IPDT64 - Start Time: 10/7/2026 5:21:57 PM

CPU1
Genuine Intel CPU Test
Module Version: 1.1.0.64b.W
Start Time: Wed Oct  7 17:21:57 2026
Test Result - PASS 
Expected: GenuineIntel
Detected: GenuineIntel
End Time: Wed Oct  7 17:21:57 2026
Total Time: in seconds: 0
--------------------------------------------------------------------
CPU1
CPU Brand String Test
Module Version: 1.1.0.64b.W
Start Time: Wed Oct  7 17:21:57 2026
Test Result - PASS 
Expected: Intel(R) Core(TM) 
Detected: Intel(R) Core(TM) i9-14900KF
Intel(R) Core(TM) processor detected..!!..
End Time: Wed Oct  7 17:21:57 2026
Total Time: in seconds: 0
--------------------------------------------------------------------
CPU1
Cache Test
Module Version: 1.1.0.64b.W
Start Time: Wed Oct  7 17:21:57 2026
Test Result - PASS

 --- Reading Cache Size ---  

- Detected L1 Data Cache Size --> 48
- Detected L1 Inst Cache Size --> 32

- Detected L2 Cache Size --> 2048
- Detected L3 Cache Size --> 36864

Cache Size Test Passed!!!

End Time: Wed Oct  7 17:21:57 2026
Total Time: in seconds: 0
--------------------------------------------------------------------
CPU1
MMXSSE Test
Module Version: 1.1.0.64b.W
Start Time: Wed Oct  7 17:21:57 2026
Test Result - PASS

DetectUtils64 DLL Version - 1.1.10

 --- Determining MMX - SSE capabilities --- 
..MMX is supported on this CPU..
..SSE is supported on this CPU..
..SSE2 is supported on this CPU..
..SSE3 is supported on this CPU..
..SSSE3 is supported on this CPU..
..SSE4.1 is supported on this CPU..
..SSE4.2 is supported on this CPU..

SSE Test Result --- PASS
SSE2 Test Result --- PASS
SSE3 Test Result --- PASS
SSSE3 Test Result --- PASS
SSE4.1 Test Result --- PASS
SSE4.2 Test Result --- PASS

End Time: Wed Oct  7 17:21:57 2026
Total Time: in seconds: 0
--------------------------------------------------------------------
CPU1
IMC Test
Module Version: 1.1.0.64b.W
Start Time: Wed Oct  7 17:21:58 2026
Test Result - PASS
--- Reading Memory Size --- 
Detected Memory Size is --> 96.00GB
--- Subtest - Memory Size Test Passed!!!  ---
--- Integrated Memory Controller Stress Test --- 
Memory to be allocated = 1048576 bytes
Memory Allocated.
Test 1 Ones and Zeros Moving Inversions write operations - Passed
Test 1 Ones and Zeros Moving Inversions verification operations - Passed
Test 2 32Bits Sliding Ones write operations - Passed
Test 2 32Bits Sliding Ones verification operations - Passed
Test 3 32Bits Sliding Zero write operations - Passed
Test 3 32Bits Sliding Zero verification operations - Passed
Memory Deallocated.
--- Subtest - Memory Stress Test Passed!!!  ---
Integrated Memory Controller Test Passed!!!
End Time: Wed Oct  7 17:21:58 2026
Total Time: in seconds: 0
--------------------------------------------------------------------
CPU1
Parallel_PrimeNum Test
Module Version: 1.0.0.13
Start Time: 10/7/2026 5:21:58 PM
Test Result - PASS
 
Module Math_PrimeNum.exe Completed - Pass

Prime Number Generation Test
Module Version: 1.1.0.64b.W
Start Time: Wed Oct  7 17:21:58 2026
DetectUtils64 DLL Version - 1.1.10
AVX is supported in your OS
Max AVX supported = AVX2
Test Result - PASS
Operation Per Second: 235500
Error: 0
--- Prime Number Generation Test Passed!!!---
End Time: Wed Oct  7 17:22:43 2026
Total Time: in seconds: 45
 
Parallel_PrimeNum
End Time: 10/7/2026 5:22:43 PM
--------------------------------------------------------------------
CPU1
Parallel_FP Test
Module Version: 1.0.0.13
Start Time: 10/7/2026 5:22:43 PM
Test Result - PASS
 
Module AVX.exe Completed - Pass
Module Math_FP.exe Completed - Pass

AVX Test
Module Version: 2.1.0.64b.W
Start Time: Wed Oct  7 17:22:43 2026
Test Result - PASS

DetectUtils64 DLL Version - 1.1.10

  --- CPU Features Detection --- 
..AVX is supported by this CPU..
..AVX2 is supported by this CPU..
..AVX512BW is NOT supported by this CPU..
..AVX512CD is NOT supported by this CPU..
..AVX512DQ is NOT supported by this CPU..
..AVX512ER is NOT supported by this CPU..
..AVX512F is NOT supported by this CPU..
..AVX512IFMA52 is NOT supported by this CPU..
..AVX512PF is NOT supported by this CPU..
..AVX512VBMI is NOT supported by this CPU..
..AVX512VL is NOT supported by this CPU..
..AES is supported by this CPU..
..PCLMULQDQ is supported by this CPU..

..AVX is supported by this Operating System..

Most Advanced AVX Feature Detected.. AVX2
AVX2 Test Result --- PASS
AES Test Result --- PASS
PCLMULQDQ Test Result --- PASS

End Time: Wed Oct  7 17:23:28 2026
Total Time: in seconds: 45

Floating Point Test
Module Version: 1.1.0.64b.W
Start Time: Wed Oct  7 17:22:43 2026
DetectUtils64 DLL Version - 1.1.10
AVX is supported in your OS
Max AVX supported = AVX2
FMA3 supported
Test Result - PASS
Million Floating Points per Second, MFLOPS: 3908.125
Error: 0
--- Floating Point Test Passed!!!---
End Time: Wed Oct  7 17:23:28 2026
Total Time: in seconds: 45
 
Parallel_FP
End Time: 10/7/2026 5:23:28 PM
--------------------------------------------------------------------
CPU1
Parallel_Math Test
Module Version: 1.0.0.13
Start Time: 10/7/2026 5:23:28 PM
Test Result - PASS
 
Module Math_PrimeNum.exe Completed - Pass
Module FMA3.exe Completed - Pass

Prime Number Generation Test
Module Version: 1.1.0.64b.W
Start Time: Wed Oct  7 17:23:28 2026
DetectUtils64 DLL Version - 1.1.10
AVX is supported in your OS
Max AVX supported = AVX2
Test Result - PASS
Operation Per Second: 235500
Error: 0
--- Prime Number Generation Test Passed!!!---
End Time: Wed Oct  7 17:24:13 2026
Total Time: in seconds: 45

FMA3 Test
Module Version: 1.1.0.64b.W
Start Time: Wed Oct  7 17:23:28 2026
Test Result - PASS

DetectUtils64 DLL Version - 1.1.10

  --- CPU Features Detection --- 
..FMA3 is supported by this CPU..
..FMA3 is supported by this Operating System..

FMA3 Test Result --- PASS

End Time: Wed Oct  7 17:24:13 2026
Total Time: in seconds: 45
 
Parallel_Math
End Time: 10/7/2026 5:24:13 PM
--------------------------------------------------------------------
CPU1
Parallel_GPUStressW Test
Module Version: 1.0.0.13
Start Time: 10/7/2026 5:24:13 PM
Test Result - PASS
 
Module Math_PrimeNum.exe Completed - Pass
Module Math_FP.exe Completed - Pass

Prime Number Generation Test
Module Version: 1.1.0.64b.W
Start Time: Wed Oct  7 17:24:13 2026
DetectUtils64 DLL Version - 1.1.10
AVX is supported in your OS
Max AVX supported = AVX2
Test Result - PASS
Operation Per Second: 235500
Error: 0
--- Prime Number Generation Test Passed!!!---
End Time: Wed Oct  7 17:24:43 2026
Total Time: in seconds: 30

Floating Point Test
Module Version: 1.1.0.64b.W
Start Time: Wed Oct  7 17:24:13 2026
DetectUtils64 DLL Version - 1.1.10
AVX is supported in your OS
Max AVX supported = AVX2
FMA3 supported
Test Result - PASS
Million Floating Points per Second, MFLOPS: 3990.87
Error: 0
--- Floating Point Test Passed!!!---
End Time: Wed Oct  7 17:24:43 2026
Total Time: in seconds: 30
 
Parallel_GPUStressW
End Time: 10/7/2026 5:24:43 PM
--------------------------------------------------------------------
CPU1
DGEMM Stress Test
Module Version: 1.1.0.64b.W
Start Time: Wed Oct  7 17:24:43 2026
Test Result - PASS

DetectUtils64 DLL Version - 1.1.10

  --- CPU Features Detection --- 
..AVX is supported by this Operating System..

Most Advanced AVX Feature Detected.. AVX2
DGEMM AVX2 Test Result --- PASS

End Time: Wed Oct  7 17:25:43 2026
Total Time: in seconds: 60
--------------------------------------------------------------------
CPU1
Frequency Check
Module Version: 1.1.0.64b.W
Start Time: Wed Oct  7 17:25:43 2026
Test Result - NO COMPARE OPTION USED
Processor Name: Intel(R) Core(TM) i9-14900KF
Measured Processor Frequency: 3.184044
End Time: Wed Oct  7 17:25:44 2026
Total Time: in seconds: 1
--------------------------------------------------------------------

System Information
------------------
Processor Name: Intel(R) Core(TM) i9-14900KF
Processor Information: Family 6 Model B7 Stepping 1
Number of Physical Cores: 24
Number of Logical Cores: 32
Operating System: Microsoft Windows 11 Pro 64-bit
Graphics Information: AMD Radeon RX 7900 XTX
--------------------------------------------------------------------

--- IPDT64 - End Time: 10/7/2026 5:25:44 PM
--- IPDT64 - Result: Pass
--------------------------------------------------------------------
