drhalftone/AuV2-SLI/sources_1/imports/RTL/uart_ctrl.v

`timescale 1ns/1ps
//==============================================================================
// uart_ctrl.v -- AuV2-SLI host control protocol (FT2232H ch.B, 0xA5 framed).
//
// Receive-side command engine that mirrors host/lauauboard.cpp byte-for-byte.
// Consumes a byte stream from uart_rx (data/valid) and produces a response
// stream to a SHARED uart_tx via a producer handshake (tx_data/tx_send/tx_busy,
// with `tx_active` telling the arbiter we own the line). All logic is in the
// clk domain (clk100); the table read ports are exposed for the pixel datapath
// (Stage 2) and the register controls (sli_ctrl) are quasi-static.
//
// Frames (SYNC = 0xA5; SYNC is NOT included in any checksum):
//   write  : A5 57 ADDR DATA CK         CK: (0x57+ADDR+DATA+CK)      == 0 mod256
//            -> 'K' ok / 'N' read-only|undefined / 'E' bad checksum
//   read   : A5 52 ADDR CK              CK: (0x52+ADDR+CK)           == 0 mod256
//            -> ADDR DATA CK2  with (ADDR+DATA+CK2)==0 ; or 'E' on bad request CK
//   upload : A5 5B TGT D[0..N-1] CK     CK: (TGT+sum(D)+CK)          == 0 mod256
//            N = 720 (TGT 0x00) / 1280 (TGT 0x01) / 256 (TGT 0x02)
//            -> 'K' ok / 'E' bad checksum|unknown target  (table committed only on 'K')
//   rdtbl  : A5 72 TGT CK               CK: (0x72+TGT+CK)            == 0 mod256
//            -> TGT D[0..N-1] CK2  with (TGT+sum(D)+CK2)==0 ; or 'E' on bad CK|target
//            (same N per TGT as upload; lets the host verify an uploaded table)
//            TGT 0x03 = EDID: 256 B of the display's captured EDID (READ-ONLY --
//            it is not an upload target; A5 5B 03 is rejected with 'E'). Always
//            256 B; if the display has no extension block, bytes 128..255 are
//            stale RAM -- byte 0x7E of block 0 is the authoritative ext count.
//
// UNDEFINED ADDRESSES ANSWER 'N', THEY DO NOT READ AS ZERO (VERSION 0x02).
//   read of an undefined address -> 'N' ADDR CK3  with ('N'+ADDR+CK3)==0
//   Same three-byte length as a good reply, so byte-stream reassembly on either
//   port is unaffected. A host tells them apart by the first byte: a good reply
//   echoes ADDR, this one starts with 'N' (0x4E). 0x4E is a DEFINED register, so a
//   read OF 0x4E can never produce the 'N' form -- the two cannot be confused.
//   Before 0x02 an undefined read returned ADDR 00 CK2: a mistyped address looked
//   exactly like a working register reading zero.
//
// Registers:
//   0x00 ID      = 0x48 'H'      (RO)        0x02 STATUS = live `led` byte (RO)
//   0x01 VERSION = 0x02          (RO)        0x06 FLAGS  = {.., usb_sw_en, lut_loaded} (RO)
//   0x08..0x0B BUILD_GIT   = {dirty, 3'b0, hash[27:0]}  (RO) -- short git hash of the source
//                            the bitstream was built from; dirty = uncommitted changes
//   0x0C..0x0F BUILD_EPOCH = unix seconds at synthesis    (RO)
//        Both are 0 when the build script did not pass them. Read them to answer "what is
//        this board running?" -- the same question the SD bitstream library has to ask.
//
//   CAMERA SETTINGS ARE READ/WRITE AT THE ADDRESS THAT REPORTS THEM (VERSION 0x02).
//   Multi-byte values: write the LOW bytes first; they are staged. Writing the
//   HIGHEST byte commits the whole value and replies 'K' (applied) or 'N' (refused).
//   Readback is the value the camera is RUNNING, from the ~10 Hz status snapshot, so
//   it can lag a commit by up to ~100 ms; staged bytes are not visible in readback.
//   Each commit is issued as the equivalent Ft+ camera opcode, so the camera module
//   validates it exactly as it validates the opcode.
//     0x40/0x41       EXPOSURE, 375 ns units         commit 0x41   (opcode 1)
//                     REFUSED ('N') if it would exceed the frame period minus the
//                     sensor reserve -- the sensor wedges past that point.
//     0x5A/0x5B/0x5C  GENLOCK DELAY, 10 ns ticks     staged
//     0x5D            {bit0 = genlock enable}        commit        (opcode 7)
//     0x8E/0x8F/0x90  TRIGGER PERIOD, 10 ns ticks    commit 0x90   (opcode 2)
//                     REFUSED if <= 1000 ticks, or if free-running and the applied
//                     exposure would no longer fit the new period.
//     0x91            FRAMES PER SCAN, 1..63         commit        (opcode 4)
//   Camera commands (write-only, read 0x00):
//     0x17 CAMCMD     bit0 = re-arm the burst capture                (opcode 3)
//     0x18/0x19       IDLE duration, ms (0 = latch)  staged, reads back staged
//     0x1A CAMIDLE    bit0 = 1 idle for 0x18/0x19 ms, 0 = release    (opcode 6)
//   0x10 PINS    = {eff_sw[3:0], phys_sw[3:0]}  (RO -- active vs physical R/G/B/orient)
//   0x14 MODEFORCE = {7:force_en, 3..0:idx}  (R/W -- pin the offline mode to idx,
//        overriding mode_select's EDID pick. For bringing up a new high-clock mode on a
//        display whose EDID would otherwise always steer to a lower-clock, higher-refresh
//        mode. force_en=0 hands control back to the EDID.)
//   0x15 LINKCTL = {7..2:secs_x2, 1:proj, 0:host}  (R/W -- disconnect pulse)
//        Write starts a self-timed disconnect: bit0 drops the HOST hot-plug
//        (hdmi_rx_hpa low -> the PC/source re-reads EDID + re-negotiates on
//        reconnect); bit1 tristates the TMDS OUTPUT (the projector loses signal
//        and re-detects on reconnect). bits[7:2] = duration in HALF-seconds
//        (1..63 -> 0.5..31.5 s). The FPGA reconnects automatically when it expires,
//        so no host follow-up is needed. Write 0x00 (or targets=0) to cancel.
//        Read 0x15 -> {proj_active, host_active, remaining_half_secs[5:0]}.
//        Example: A5 57 15 19 CK drops the host for 3 s (0x19 = secs_x2=6, host=1).
//   0x13 SLICTRL = {7:sw_en, 6:mode_en, 5:mode_val, 3:R,2:G,1:B,0:orient}  (R/W)
//        sw_en   : USB drives R/G/B/orient instead of the physical SW[3:0] pins.
//        mode_en : USB drives the SLI pattern enable instead of the camera "mode" GPIO
//                  (C1_in[1]). That pin is PULLED LOW in the XDC ("default passthrough
//                  for colour-bar test"), so with no camera board attached pattern_gen
//                  is off and the vga colour bars just pass through. Set mode_en=1,
//                  mode_val=1 to turn the SLI fringes on over USB with no camera.
//        Note the corr transfer LUT (target 0x02) only shapes FRINGE pixels, so it has
//        no visible effect until the pattern generator is actually enabled.
//
//   Offline-mode decision (RO) -- what mode_select picked from the display's EDID,
//   and what it had to pick from. Without these the choice is unobservable: you can
//   only infer it by decoding the EDID by hand and measuring the frame rate.
//   0x20 MODE    = {7:valid, 6:edid_ok, 3..0:mode_idx}   curated-table index in use
//   0x21 REFR    = refresh in Hz
//   0x22 / 0x23  = h_active  lo / hi (12-bit)
//   0x24 / 0x25  = v_active  lo / hi (12-bit)
//   0x26 / 0x27 / 0x28 = pixel clock in kHz, lo / mid / hi (17-bit)
//   0x29 / 0x2A  = supported-mode mask, lo / hi (13-bit; bit i = table index i)
//==============================================================================
module uart_ctrl #(
    parameter [7:0] ID_MAGIC = 8'h48,    // 'H'
    parameter [7:0] VERSION  = 8'h02,         // 0x02: 'N' on undefined reads, camera regs R/W
    // Build identity (regs 0x08..0x0F), passed down from the build script. Integers,
    // not vectors, so they cross the VHDL top unchanged: a 7-hex-digit git hash is 28
    // bits and unix seconds fit 31 bits until 2038 -- both inside a VHDL integer.
    parameter integer BUILD_GIT   = 0,
    parameter integer BUILD_DIRTY = 0,
    parameter integer BUILD_EPOCH = 0,
    // Sensor reserve subtracted from the frame period before exposure -- MUST match
    // usb_link's RESERVE_TICKS (44.1 us measured gap + 10 us margin), which computes
    // the published max exposure from the same number.
    parameter [23:0] RESERVE_TICKS = 24'd5410,
    parameter integer CLK_HZ = 100_000_000,   // clk rate -> LINKCTL half-second tick
    // camera line-buffer readback length (bytes) and its address width. Default is the real
    // 1280-pixel line; the testbench overrides it small so a full UART read stays fast.
    parameter integer CAM_LINE_LEN = 1280,
    parameter integer CAM_LINE_AW  = 11
)(
    input  wire        clk,
    input  wire        rst,

    // ---- from uart_rx ----
    input  wire [7:0]  rx_data,
    input  wire        rx_valid,

    // ---- to the shared uart_tx (via arbiter) ----
    output reg  [7:0]  tx_data,
    output reg         tx_send,
    input  wire        tx_busy,
    output wire        tx_active,        // high while we own/need the TX line

    // ---- live status surfaced through registers ----
    input  wire [7:0]  led,    // reg 0x02 -- video/camera handshake byte
    input  wire [7:0]  pins,   // reg 0x10 -- {eff_sw[3:0], phys_sw[3:0]} (active vs physical switches)

    // ---- quasi-static control outputs (Stage 2: drive pixel_pipe) ----
    output reg  [7:0]  sli_ctrl,         // register 0x13
    // reg 0x16 CAMSIM {7:rdy_en, 0:rdy_val} -- drive the camera-ready GPIO from
    // the host. `rdy` is a pin from the old DB9 camera board and NOTHING drives
    // it in the PYTHON1300 stack, so the pacing logic it feeds was untestable.
    // An untestable fix is an unverified fix.
    output reg  [7:0]  cam_sim,
    output wire        sli_ctrl_en,      // = sli_ctrl[7]  (USB overrides switches)
    output wire        lut_loaded,       // a table has been uploaded since reset

    // ---- table read ports (Stage 2: read by the pattern datapath) ----
    // Defaulted in the VHDL component decl so the top can leave them open for now.
    input  wire [7:0]  corr_addr,  output reg [7:0] corr_dout,   // 256-entry correction
    // VESTIGIAL, both of them. Au2_SLI ties lut_addr/lutv_addr to 0 and leaves the
    // douts open -- "vestigial from the old indexMap/LUT ROM design". Nothing in the
    // datapath reads either table; they remain only as host-writable storage.
    // They were labelled "row cosine"/"col cosine" here, which is not what they are
    // and not what they were for. THE LIVE LINEARISATION TABLE IS corr (target 0x02,
    // 256 entries, one per grey level), applied as out = corr[cos] in pattern_gen --
    // that is what makes a 0..255 ramp come out linear on the display.
    input  wire [9:0]  lut_addr,   output reg [7:0] lut_dout,    // 720 B, unused
    input  wire [10:0] lutv_addr,  output reg [7:0] lutv_dout,   // 1280 B, unused

    // ---- captured-EDID read port (TGT_EDID) ----
    // Unlike the tables above, this RAM lives in edid_merge, so we DRIVE the
    // address outward and the data comes back registered one clock later --
    // the same latency as the local RAMs, so S_RTAB needs no special-casing.
    output wire [7:0]  edid_rd_addr,
    input  wire [7:0]  edid_rd_data,

    // ---- SERVED-EDID read port (TGT_EDID_SRV, rdtbl 0x05) ----
    // TGT_EDID above is what the DISPLAY sent us. This is the merged block we
    // SERVE to the PC -- the two differ by the pass-through window filter, and
    // being unable to see the served copy meant the merge could only be checked
    // against Windows' registry cache, which is the host's stale copy rather
    // than what the fabric is actually presenting on the DDC.
    output wire [7:0]  esrv_rd_addr,
    input  wire [7:0]  esrv_rd_data,

    // ---- captured camera-line read port (TGT_CAM_LINE, rdtbl 0x04) ----
    // Same external-RAM pattern as TGT_EDID: the line buffer lives in cam_line_buf.
    output wire [CAM_LINE_AW-1:0] cam_line_addr,
    input  wire [7:0]             cam_line_data,

    // ---- offline mode decision (regs 0x20..0x2A, read-only) ----
    // What mode_select chose from the display's EDID, and what it had to choose
    // from. Quasi-static: only changes when a new EDID is parsed. Caller supplies
    // these already in this clock domain.
    input  wire [3:0]  mode_idx_i,      // applied curated-table index
    input  wire        mode_valid_i,    // a mode has been picked
    input  wire        mode_edid_ok_i,  // display EDID block-0 checksum good
    input  wire [7:0]  mode_refr_i,     // refresh (Hz)
    input  wire [11:0] mode_hact_i,     // active pixels
    input  wire [11:0] mode_vact_i,     // active lines
    input  wire [16:0] mode_pclk_i,     // pixel clock (kHz)
    input  wire [13:0] mode_supp_i,     // 14-bit supported-mode mask

    // ---- radiometric transfer LUT, live in the PIXEL datapath ----
    // pattern_gen's LUT seam: it presents the raw cosine value and consumes the
    // linearized one in the SAME pipeline stage (pat_out = flash_d ? pat : lut_dout),
    // so this read must be COMBINATIONAL -- a registered BRAM read would apply each
    // pixel's correction to the next pixel. Async read => Vivado infers distributed
    // RAM (256x8 LUTRAM), which is what we want.
    //
    // Clock domains: written on clk (clk100) during an upload, read continuously from
    // pixel_clk. No handshake -- a table upload takes a few ms and tears the curve for
    // that window (a few pixels get a mix of old/new). Upload while not scanning.
    input  wire [7:0]  corr_pat_addr,
    output wire [7:0]  corr_pat_dout,

    // ---- MODEFORCE (reg 0x14, R/W) -- bring-up / bring-down of new modes ----
    // {7:force_en, 3..0:idx}. When force_en=1 the host pins the offline mode to idx
    // instead of whatever mode_select picked from the EDID. Needed because the pick is
    // refresh-first: a display that supports BOTH 1024x768@75 and 1280x1024@60 will
    // always choose the 75 Hz mode, so a new high-pixel-clock mode can never be reached
    // -- and therefore never tested -- on such a display without forcing it.
    output reg  [7:0]  mode_force,

    // ---- LINKCTL (reg 0x15): host / projector hot-plug disconnect pulse ----
    // Self-timed: the command carries a duration, and the FPGA holds the disconnect
    // for that long then reconnects on its own (so a host crash can never leave the
    // links dead). link_drop_host forces hdmi_rx_hpa low (host re-negotiates on
    // reconnect); link_drop_proj tristates the TMDS output (projector sees no signal).
    output reg         link_drop_host,
    output reg         link_drop_proj,

    // ---- PYTHON 1300 SPI mailbox (regs 0x30..0x36) ----
    // A sensor SPI transaction is 9-bit address + 16-bit data, which does not fit the
    // 1-byte register model. So the host stages the operands across registers, then fires:
    //
    //   0x30 W  addr[7:0]
    //   0x31 W  {rw, 6'b0, addr[8]}      rw: 1 = write, 0 = read
    //   0x32 W  wdata[7:0]               (writes only)
    //   0x33 W  wdata[15:8]              (writes only)
    //   0x34 W  GO -- any value fires the transaction and clears `done`
    //   0x34 R  {busy, done, 6'b0}       poll until busy=0, done=1
    //   0x35 R  rdata[7:0]               (reads only)
    //   0x36 R  rdata[15:8]
    //
    // 0x30..0x33 read back what was staged, so the host can verify before firing.
    output reg  [8:0]  cam_spi_addr,
    output reg         cam_spi_rw,
    output reg  [15:0] cam_spi_wdata,
    output reg         cam_spi_start,     // 1-clk strobe
    input  wire [15:0] cam_spi_rdata,
    // M4: camera datapath status, 8 bytes at 0x3A..0x41. Read-only, and already
    // captured on a stable snapshot upstream -- see cam_frame_ft's cstat_r.
    input  wire [223:0] cam_stat_i,
    // G0: vsync period measured at 100 MHz -- {max, min, last}, 24 bits each.
    // The master clock genlock would lock to; its stability bounds the
    // achievable lock quality. Regs 0x4A..0x52.
    input  wire [71:0]  vs_per_i,

    // ---- INCOMING (pass-through) HDMI timing, measured (regs 0x60..0x67) ----
    // From video_meas. Distinct from 0x22..0x25, which report the OFFLINE mode
    // chosen out of the display's EDID -- those answer "what can I send", these
    // answer "what am I being sent". They disagree whenever the PC picks a mode
    // other than the one mode_select would have, which is the normal case.
    //   [11:0] h_active   [23:12] v_active   [47:24] frame period (10 ns)
    //   [48] meas_ok      [49] vid_valid
    input  wire [55:0]  rx_meas_i,
    // Recovered pixel clock in kHz (regs 0x68..0x6A). Reported because the
    // pass-through failure on the Pt cannot be diagnosed without it.
    input  wire [17:0]  rx_pixkhz_i,
    // RX diagnostics (reg 0x6B): IDELAYCTRL ready plus the per-channel
    // invalid-symbol flags hdmi_input computes and hdmi_io used to drop.
    input  wire [7:0]   rx_diag_i,
    // video_phase_fifo re-prime count (reg 0x6C). Static = healthy.
    input  wire [7:0]   vfifo_rep_i,
    // Inter-channel control-period coincidence (regs 0x6D..0x70).
    input  wire [31:0]  ctl_diag_i,
    input  wire [31:0]  vdp_diag_i,
    input  wire [31:0]  pre_diag_i,
    input  wire [31:0]  gb_diag_i,
    input  wire [31:0]  evt_diag_i,
    input  wire [31:0]  hpd_diag_i,
    input  wire [55:0]  out_meas_i,
    input  wire [17:0]  out_pixkhz_i,
    // G0: max usable exposure for the CURRENT frame rate, computed in
    // usb_link from the measured vsync period and the measured sensor gap.
    // {reserve_ticks[15:0], valid, reg_limited, 6'b0, max_expo[15:0]}
    input  wire [39:0]  maxexp_i,
    // ---- camera commands issued by register writes (clk domain) ----
    // One Ft+ opcode word per commit, {opcode[31:28], payload[27:0]}, with a 1-clk
    // strobe. cam_frame_ft merges it into the decoder the Ft+ opcodes already use.
    output reg  [31:0] cam_cmd_word,
    output reg         cam_cmd_valid,
    // LIVE camera settings, NOT the 10 Hz snapshot: {gl_live, trig_per[23:0],
    // expo_cur[15:0]}. The exposure/period safety checks must see a commit that
    // landed a few ms ago -- against the snapshot, "raise exposure, then shorten
    // the period" inside 100 ms would pass both checks and wedge the sensor.
    // All zeros with no camera, which refuses every exposure commit.
    input  wire [40:0]  cam_live_i,
    input  wire        cam_spi_busy,
    input  wire        cam_spi_done,      // 1-clk strobe from cam_spi_master

    // ---- PYTHON 1300 discrete pins (regs 0x37/0x38) ----
    //   0x37 RW {reset_n, 4'b0, trigger[2:0]}
    //   0x38 R  {6'b0, monitor[1:0]}
    //
    // reset_n is bit 7 and RESETS TO 0 -- the sensor stays in reset until the host
    // explicitly releases it. That matches the board, which pulls reset_n low externally
    // so the part is held in reset through the entire FPGA configuration window.
    output reg  [7:0]  cam_gpio,
    input  wire [7:0]  cam_gpio_in,

    // ---- PYTHON 1300 boot sequencer (reg 0x39) ----
    //   0x39 W  GO -- any value starts the ROM-driven boot; dropped ('N') if already busy
    //   0x39 R  {4'b0, ready, busy, failed, pll_timeout}
    // The sequencer (cam_boot_seq) owns the SPI master + cam_reset_n while busy; the Qt
    // tool fires this AFTER a chip-ID read, then polls 0x39 until ready (or failed).
    output reg         cam_boot_go,       // 1-clk strobe
    input  wire [3:0]  cam_boot_stat      // {ready, busy, failed, pll_timeout}
);
    // ---- protocol constants ----
    localparam [7:0] SYNC = 8'hA5;
    localparam [7:0] OP_W = 8'h57, OP_R = 8'h52, OP_L = 8'h5B, OP_LR = 8'h72;  // W R upload read-table('r')
    localparam [7:0] ACK_K = 8'h4B, ACK_E = 8'h45, ACK_N = 8'h4E;
    localparam [7:0] TGT_LUT = 8'h00, TGT_LUTV = 8'h01, TGT_CORR = 8'h02;
    localparam [7:0] TGT_EDID = 8'h03;       // read-only: the display's captured EDID
    localparam [7:0] TGT_CAM_LINE = 8'h04;   // read-only: one captured camera line (task #11)
    localparam [7:0] TGT_EDID_SRV = 8'h05;   // read-only: the MERGED EDID we serve to the PC

    // ---- table RAMs (write-through during upload; read ports for Stage 2) ----
    reg [7:0] corr [0:255];
    reg [7:0] lut  [0:719];
    reg [7:0] lutv [0:1279];

    // corr powers up as IDENTITY (corr[i] = i), not zero. It is now live in the pixel
    // datapath (pattern_gen's radiometric transfer LUT), so an all-zero power-up would
    // black the pattern out until a table was uploaded. Identity == no correction.
    integer ci;
    initial for (ci = 0; ci < 256; ci = ci + 1) corr[ci] = ci[7:0];

    // Combinational (async) read into the pixel datapath -- see the port comment.
    assign corr_pat_dout = corr[corr_pat_addr];

    // ---- loaded flags ----
    reg corr_ld = 1'b0, lut_ld = 1'b0, lutv_ld = 1'b0;
    assign lut_loaded  = corr_ld | lut_ld | lutv_ld;
    assign sli_ctrl_en = sli_ctrl[7];

    // ---- readback (read-table) addressing ----
    // During a readback the table RAMs are addressed by rd_idx; otherwise by the
    // external Stage-2 read ports. UART byte time (~8680 clk) dwarfs the 1-cycle
    // BRAM read latency, so the byte is always settled before it is sent.
    reg [11:0] rd_idx   = 12'd0;
    reg        rb_active = 1'b0;
    reg [1:0]  rb_ph    = 2'd0;   // 0=target prologue, 1=data, 2=checksum

    // ---- camera SPI result latch ----
    // cam_spi_master's rdata/done are transient; the host polls over a UART that is
    // ~4 orders of magnitude slower than the transaction. So latch the result and keep
    // a sticky `done` that a fresh GO clears.
    reg [15:0] cam_rdata_l = 16'd0;
    reg        cam_done_l  = 1'b0;

    // ---- LINKCTL self-timer (reg 0x15) ----
    localparam integer HALF_SEC = CLK_HZ/2;      // clk ticks per half-second
    reg [25:0] link_presc  = 26'd0;              // 0..HALF_SEC-1 (2^26 = 67M > 50M)
    reg [5:0]  link_secs   = 6'd0;               // remaining half-seconds
    reg [1:0]  link_tgt    = 2'd0;               // {proj, host}
    reg        link_active = 1'b0;

    // ---- camera settings: staged low bytes (see the header) ----
    reg [7:0]  expo_lo_s = 8'd0;
    reg [15:0] trig_lo_s = 16'd0;
    reg [23:0] gl_dly_s  = 24'd0;
    reg [15:0] idle_ms_s = 16'd0;

    wire        live_gl   = cam_live_i[40];
    wire [23:0] live_trig = cam_live_i[39:16];
    wire [15:0] live_expo = cam_live_i[15:0];

    // Exposure units (375 ns) -> 10 ns ticks is x37.5 = (x*75)>>1. Shifts, not a
    // multiplier: 75 = 64 + 8 + 2 + 1. Floor loses under one tick against the 10 us
    // margin inside RESERVE_TICKS.
    function [22:0] expo_ticks(input [15:0] e);
        reg [22:0] x;
        begin
            x = {7'd0, e};
            expo_ticks = ((x << 6) + (x << 3) + (x << 1) + x) >> 1;
        end
    endfunction

    // ---- FSM ----
    localparam [3:0]
        S_SYNC  = 4'd0,  S_OP    = 4'd1,
        S_WADDR = 4'd2,  S_WDATA = 4'd3,  S_WCK = 4'd4,
        S_RADDR = 4'd5,  S_RCK   = 4'd6,
        S_UTGT  = 4'd7,  S_UDATA = 4'd8,  S_UCK = 4'd9,
        S_RESP  = 4'd10,
        S_RTGT  = 4'd11, S_RTCK  = 4'd12, S_RTAB = 4'd13;

    // INTER-BYTE TIMEOUT -- a stalled frame must not own the link forever.
    //
    // Without this, a host that dies part-way through a table upload leaves the
    // FSM counting payload bytes that never arrive, and it swallows EVERYTHING
    // after -- including well-formed register reads -- until the outstanding
    // length happens to be satisfied. Found by stress test: abandoning a
    // 1280-byte upload after 5 bytes killed the control plane indefinitely, and
    // only feeding the remaining 1,275 bytes brought it back. That is reachable
    // by accident -- Ctrl-C during upload_corr.py does it -- and the host has no
    // way to know the cure.
    //
    // At 115200 baud one byte is ~87 us, so a gap of this length inside a frame
    // is unambiguous: the sender is gone. Abort and resync on the next SYNC.
    // Only armed OUTSIDE S_SYNC, so an idle link is never disturbed.
    localparam integer RX_IDLE_TICKS = CLK_HZ / 20;   // 50 ms
    reg [$clog2(RX_IDLE_TICKS+1)-1:0] rx_idle = 0;
    reg        rx_timeout = 1'b0;

    reg [3:0]  state = S_SYNC;
    reg [7:0]  addr, dbyte, sum8;
    reg [11:0] cnt, len;             // up to 1280
    reg [2:0]  tgt;                  // 0=lut 1=lutv 2=corr 3=edid 4=cam_line

    // readback byte source (selected by target)
    wire [7:0] rb_dout = (tgt == 3'd5) ? esrv_rd_data  :
                         (tgt == 3'd4) ? cam_line_data :
                         (tgt == 3'd3) ? edid_rd_data  :
                         (tgt == 3'd2) ? corr_dout     :
                         (tgt == 3'd1) ? lutv_dout     : lut_dout;

    // EDID RAM address (external, in edid_merge). Only sampled while we are
    // streaming TGT_EDID; harmless otherwise -- it is a pure read port.
    assign edid_rd_addr = rd_idx[7:0];
    assign esrv_rd_addr = rd_idx[7:0];

    // Camera line-buffer read port (external, in cam_line_buf). Same TGT_EDID pattern:
    // drive the address out, take registered data back one clock later.
    assign cam_line_addr = rd_idx[CAM_LINE_AW-1:0];

    // response buffer (1 or 3 bytes)
    reg [7:0]  resp [0:2];
    reg [1:0]  resp_len, resp_idx;

    assign tx_active = (state == S_RESP) || (state == S_RTAB);

    // synchronous table read ports (kept always -> RAMs are not optimised away).
    // Address from rd_idx during a readback stream, else from the Stage-2 ports.
    wire [7:0]  corr_ra = rb_active ? rd_idx[7:0]  : corr_addr;
    wire [9:0]  lut_ra  = rb_active ? rd_idx[9:0]  : lut_addr;
    wire [10:0] lutv_ra = rb_active ? rd_idx[10:0] : lutv_addr;
    always @(posedge clk) begin
        corr_dout <= corr[corr_ra];
        lut_dout  <= lut[lut_ra];
        lutv_dout <= lutv[lutv_ra];
    end

    // ---- register read mux ----
    //
    // A COMBINATIONAL ALWAYS BLOCK, not a function called from a continuous assign.
    //
    // This used to be `wire [7:0] rd_data = regread(addr);`. In xsim that re-evaluates
    // only when the function's ARGUMENT changes -- every signal the function reads
    // internally (sli_ctrl, pins, cam_gpio, cam_done_l, ...) is invisible to its
    // sensitivity list. So a host that writes a register and then reads the SAME address
    // gets a STALE value back, with a stale-but-self-consistent checksum, so the reply
    // looks perfectly valid. Polling reg 0x34 for SPI completion does exactly that and
    // hung forever. `always @*` did not fix it -- xsim does not look inside the function
    // there either.
    //
    // Synthesis inferred the correct mux either way, so hardware was fine and only the
    // model lied. That is worse than a plain bug: the bench agrees with you while the
    // silicon does something else. Written out flat, the sensitivity is unambiguous
    // everywhere.
    reg [7:0] rd_data;
    reg       rd_def;                 // 0 = no such register -> 'N' reply
    wire [27:0] build_git   = BUILD_GIT;
    wire [31:0] build_epoch = BUILD_EPOCH;
    always @* begin
        rd_data = 8'h00;
        rd_def  = 1'b1;
case (addr)
            8'h00:   rd_data  = ID_MAGIC;
            8'h01:   rd_data  = VERSION;
            8'h02:   rd_data  = led;
            8'h06:   rd_data  = {6'b0, sli_ctrl[7], (corr_ld | lut_ld | lutv_ld)};
            // ---- build identity ----
            8'h08:   rd_data  = build_git[7:0];
            8'h09:   rd_data  = build_git[15:8];
            8'h0A:   rd_data  = build_git[23:16];
            8'h0B:   rd_data  = {(BUILD_DIRTY != 0), 3'b0, build_git[27:24]};
            8'h0C:   rd_data  = build_epoch[7:0];
            8'h0D:   rd_data  = build_epoch[15:8];
            8'h0E:   rd_data  = build_epoch[23:16];
            8'h0F:   rd_data  = build_epoch[31:24];
            8'h10:   rd_data  = pins;
            8'h13:   rd_data  = sli_ctrl;
            8'h14:   rd_data  = mode_force;
            8'h15:   rd_data  = {link_drop_proj, link_drop_host, link_secs};
            8'h16:   rd_data  = cam_sim;
            // ---- camera commands: write-only strobes read 0, the staged duration reads back
            8'h17:   rd_data  = 8'h00;
            8'h18:   rd_data  = idle_ms_s[7:0];
            8'h19:   rd_data  = idle_ms_s[15:8];
            8'h1A:   rd_data  = 8'h00;
            // ---- offline mode decision (read-only) ----
            8'h20:   rd_data  = {mode_valid_i, mode_edid_ok_i, 2'b0, mode_idx_i};
            8'h21:   rd_data  = mode_refr_i;
            8'h22:   rd_data  = mode_hact_i[7:0];
            8'h23:   rd_data  = {4'b0, mode_hact_i[11:8]};
            8'h24:   rd_data  = mode_vact_i[7:0];
            8'h25:   rd_data  = {4'b0, mode_vact_i[11:8]};
            8'h26:   rd_data  = mode_pclk_i[7:0];
            8'h27:   rd_data  = mode_pclk_i[15:8];
            8'h28:   rd_data  = {7'b0, mode_pclk_i[16]};
            8'h29:   rd_data  = mode_supp_i[7:0];
            8'h2A:   rd_data  = {2'b0, mode_supp_i[13:8]};
            // ---- PYTHON 1300 SPI mailbox ----
            8'h30:   rd_data  = cam_spi_addr[7:0];
            8'h31:   rd_data  = {cam_spi_rw, 6'b0, cam_spi_addr[8]};
            8'h32:   rd_data  = cam_spi_wdata[7:0];
            8'h33:   rd_data  = cam_spi_wdata[15:8];
            8'h34:   rd_data  = {cam_spi_busy, cam_done_l, 6'b0};
            8'h35:   rd_data  = cam_rdata_l[7:0];
            8'h36:   rd_data  = cam_rdata_l[15:8];
            // ---- PYTHON 1300 discrete pins ----
            8'h37:   rd_data  = cam_gpio;
            8'h38:   rd_data  = cam_gpio_in;
            8'h39:   rd_data  = {4'b0, cam_boot_stat};   // {ready, busy, failed, pll_timeout}
            // ---- 0x3A..0x41: CAMERA DATAPATH STATUS (M4) ----------------
            // The camera used to report only over its own 1 Mbaud UART, which
            // meant Port A could show the SLI plane OR the camera, never both.
            // Worse, the frame stream on Port B goes SILENT exactly when the
            // camera fails -- so its health could not be read in the one
            // situation that needed it.
            //   0x3A {stw[2:0], rd_busy, calib, aligned, streaming, cap}
            //   0x3B {cfifo_ovf, ufifo_ovf, ufifo_empty, txe, 0000}
            //   0x3C/0x3D ldrop lo/hi   -- padded frames; static == none lost
            //   0x3E/0x3F frame period / 16, in 72 MHz wordclk cycles
            //   0x40/0x41 exposure0 lo/hi, in 375 ns units
            8'h3A:   rd_data  = cam_stat_i[7:0];
            8'h3B:   rd_data  = cam_stat_i[15:8];
            8'h3C:   rd_data  = cam_stat_i[23:16];
            8'h3D:   rd_data  = cam_stat_i[31:24];
            8'h3E:   rd_data  = cam_stat_i[39:32];
            8'h3F:   rd_data  = cam_stat_i[47:40];
            8'h40:   rd_data  = cam_stat_i[55:48];
            8'h41:   rd_data  = cam_stat_i[63:56];
            // ---- 0x42..0x49: MONITOR-PIN TIMESTAMPS (genlock G0) ------------
            // How long after the trigger edge the sensor actually starts
            // integrating, from monitor0 (= Integration Time, monitor_select 0x1
            // in reg 192[13:11], which the boot ROM already sets).
            //
            //   0x42/0x43/0x44  trigger -> integration start, MINIMUM, 10 ns units
            //   0x45/0x46/0x47  same, MAXIMUM
            //   0x48/0x49       last integration length, 160 ns units
            //
            // MIN AND MAX ARE THE POINT. The datasheet gives no trigger-to-
            // exposure delay at all, and says the start snaps to a line boundary
            // (~5.7 us) whenever integration begins during a readout -- which in
            // pipelined mode is always. max-min IS that jitter, measured. A
            // single sample could not show it.
            //
            // The window resets every status tick (~10 Hz), so each read
            // describes a fresh ~12-frame window rather than a high-water mark
            // that only ever widens.
            8'h42:   rd_data  = cam_stat_i[71:64];
            8'h43:   rd_data  = cam_stat_i[79:72];
            8'h44:   rd_data  = cam_stat_i[87:80];
            8'h45:   rd_data  = cam_stat_i[95:88];
            8'h46:   rd_data  = cam_stat_i[103:96];
            8'h47:   rd_data  = cam_stat_i[111:104];
            8'h48:   rd_data  = cam_stat_i[119:112];
            8'h49:   rd_data  = cam_stat_i[127:120];
            // ---- 0x4A..0x52: VSYNC PERIOD (genlock G0) --------------------
            //   0x4A/0x4B/0x4C  last period, 10 ns units
            //   0x4D/0x4E/0x4F  minimum over the status window
            //   0x50/0x51/0x52  maximum over the status window
            // max-min IS the master's jitter. `N=` in the telemetry line is an
            // edge COUNT and dithers between 51 and 52 at 120 Hz, so it cannot
            // resolve the period better than ~2% and cannot see jitter at all.
            8'h4A:   rd_data  = vs_per_i[7:0];
            8'h4B:   rd_data  = vs_per_i[15:8];
            8'h4C:   rd_data  = vs_per_i[23:16];
            8'h4D:   rd_data  = vs_per_i[31:24];
            8'h4E:   rd_data  = vs_per_i[39:32];
            8'h4F:   rd_data  = vs_per_i[47:40];
            8'h50:   rd_data  = vs_per_i[55:48];
            8'h51:   rd_data  = vs_per_i[63:56];
            8'h52:   rd_data  = vs_per_i[71:64];
            // ---- 0x53..0x57: MAX USABLE EXPOSURE (answer to "how long can
            // I expose at this frame rate?") -----------------------------
            //   0x53/0x54  max exposure in EXPOSURE REGISTER UNITS -- write
            //              this straight back with opcode 1, no conversion
            //   0x55       {7: valid, 6: limited by the 16-bit register
            //              rather than by the frame period}
            //   0x56/0x57  the reserve subtracted, in 10 ns ticks
            //
            // valid = 0 means the vsync period was not plausible (no edges,
            // counter saturated). DO NOT fall back to a default in that case:
            // commanding an exposure longer than the frame period wedges the
            // sensor until the FPGA is reconfigured, which is the exact
            // failure this register exists to prevent.
            8'h53:   rd_data  = maxexp_i[7:0];
            8'h54:   rd_data  = maxexp_i[15:8];
            8'h55:   rd_data  = maxexp_i[23:16];
            8'h56:   rd_data  = maxexp_i[31:24];
            8'h57:   rd_data  = maxexp_i[39:32];
            // ---- 0x58/0x59: G1 -- ext_sync edge count, free-running, wraps.
            // Read twice and check it moved: that is G1's functional proof
            // that the projector's vsync actually reaches cam_frame_ft.
            8'h58:   rd_data  = cam_stat_i[135:128];
            8'h59:   rd_data  = cam_stat_i[143:136];
            // ---- 0x5A..0x5D: G3 VSYNC -> TRIGGER DELAY (readback) -----------
            // The delay is set over the Ft+ (opcode 7) but must be readable here,
            // because Port A is the link that still answers when Port B is silent.
            //   0x5A/0x5B/0x5C  delay, 10 ns ticks (24-bit, 0..167 ms)
            //   0x5D  {6'b0, gl_live, gl_en}
            // gl_en is what was COMMANDED; gl_live is whether ext_sync is actually
            // arriving. They differ exactly when the display has gone away and the
            // trigger has fallen back to free-running -- which is the state worth
            // being able to see.
            8'h5A:   rd_data  = cam_stat_i[151:144];
            8'h5B:   rd_data  = cam_stat_i[159:152];
            8'h5C:   rd_data  = cam_stat_i[167:160];
            8'h5D:   rd_data  = cam_stat_i[175:168];
            // 0x5E outstanding triggers, 0x5F FIFO overflows (saturates).
            // OUTSTANDING IS NOT DIAGNOSTIC PADDING. With a delay longer than one
            // frame the capture of pattern k lands while pattern k+floor(D/T) is on
            // screen -- every frame is present and the rate is full, but the PAIRING
            // is offset. The host must read that offset here rather than assume it:
            // an assumed offset wrong by one yields a phase map that looks plausible
            // and is wrong everywhere.
            8'h5E:   rd_data  = cam_stat_i[183:176];
            8'h5F:   rd_data  = cam_stat_i[191:184];
            // ---- 0x60..0x67: INCOMING HDMI TIMING, measured ---------------
            // What the SOURCE is sending, from video_meas. Read 0x67 FIRST: if
            // meas_ok is 0 the other six read 0 on purpose, because a stale
            // resolution that looks live is worse than no answer.
            //   frame rate Hz = 1e8 / period(0x64..0x66)
            8'h60:   rd_data  = rx_meas_i[7:0];             // h_active lo
            8'h61:   rd_data  = {4'b0, rx_meas_i[11:8]};    // h_active hi
            8'h62:   rd_data  = rx_meas_i[19:12];           // v_active lo
            8'h63:   rd_data  = {4'b0, rx_meas_i[23:20]};   // v_active hi
            8'h64:   rd_data  = rx_meas_i[31:24];           // period lo  (10 ns)
            8'h65:   rd_data  = rx_meas_i[39:32];           // period mid
            8'h66:   rd_data  = rx_meas_i[47:40];           // period hi
            8'h67:   rd_data  = {6'b0, rx_meas_i[49], rx_meas_i[48]};  // {vid_valid, meas_ok}
            8'h68:   rd_data  = rx_pixkhz_i[7:0];            // recovered pclk kHz lo
            8'h69:   rd_data  = rx_pixkhz_i[15:8];           // ...mid
            8'h6A:   rd_data  = {6'b0, rx_pixkhz_i[17:16]};  // ...hi
            // 0x6B RX DIAG: [6]idelay_rdy [5]ch2_inv [4]ch1_inv [3]ch0_inv
            //               [2]dvid_mode  [1]pll_locked [0]symbol_sync
            8'h6B:   rd_data  = rx_diag_i;
            8'h6C:   rd_data  = vfifo_rep_i;   // phase-FIFO re-primes
            // 0x6D/0x6E ch0 ctl cycles per 65536-pixel window
            // 0x6F/0x70 cycles where ALL THREE channels are in ctl together
            8'h6D:   rd_data  = ctl_diag_i[7:0];
            8'h6E:   rd_data  = ctl_diag_i[15:8];
            8'h6F:   rd_data  = ctl_diag_i[23:16];
            8'h70:   rd_data  = ctl_diag_i[31:24];
            8'h71:   rd_data  = vdp_diag_i[7:0];
            8'h72:   rd_data  = vdp_diag_i[15:8];
            8'h73:   rd_data  = vdp_diag_i[23:16];
            8'h74:   rd_data  = vdp_diag_i[31:24];
            8'h75:   rd_data  = pre_diag_i[7:0];
            8'h76:   rd_data  = pre_diag_i[15:8];
            8'h77:   rd_data  = pre_diag_i[23:16];
            8'h78:   rd_data  = pre_diag_i[31:24];
            8'h79:   rd_data  = gb_diag_i[7:0];
            8'h7A:   rd_data  = gb_diag_i[15:8];
            8'h7B:   rd_data  = gb_diag_i[23:16];
            8'h7C:   rd_data  = gb_diag_i[31:24];
            8'h7D:   rd_data  = evt_diag_i[7:0];
            8'h7E:   rd_data  = evt_diag_i[15:8];
            8'h7F:   rd_data  = evt_diag_i[23:16];
            8'h80:   rd_data  = evt_diag_i[31:24];
            8'h81:   rd_data  = hpd_diag_i[7:0];    // HPD-to-PC falling edges
            8'h82:   rd_data  = hpd_diag_i[15:8];   // edid_ok falling edges
            // ---- OUTGOING raster: UNPACKED exactly like 0x60..0x67 above. ----
            // video_meas packs 12-bit h, 12-bit v and a 24-bit period, so a raw
            // byte-for-byte copy straddles the field boundaries and reports
            // nonsense (33568x15653 was the first attempt). Mirror the input map.
            8'h83:   rd_data  = out_meas_i[7:0];              // h_active lo
            8'h84:   rd_data  = {4'b0, out_meas_i[11:8]};     // h_active hi
            8'h85:   rd_data  = out_meas_i[19:12];            // v_active lo
            8'h86:   rd_data  = {4'b0, out_meas_i[23:20]};    // v_active hi
            8'h87:   rd_data  = out_meas_i[31:24];            // period lo (10 ns)
            8'h88:   rd_data  = out_meas_i[39:32];            // period mid
            8'h89:   rd_data  = out_meas_i[47:40];            // period hi
            8'h8A:   rd_data  = {6'b0, out_meas_i[49], out_meas_i[48]}; // {valid, ok}
            8'h8B:   rd_data  = out_pixkhz_i[7:0];            // transmitted pclk kHz
            8'h8C:   rd_data  = out_pixkhz_i[15:8];
            8'h8D:   rd_data  = {6'b0, out_pixkhz_i[17:16]};
            // 0x8E..0x90: the FREE-RUNNING trigger period (opcode 2), 10 ns ticks.
            // Previously unreadable, which is why max-exposure had to be inferred
            // from two other registers. 0x55 bit 5 says which period the max-exposure
            // answer was computed from.
            8'h8E:   rd_data  = cam_stat_i[199:192];
            8'h8F:   rd_data  = cam_stat_i[207:200];
            8'h90:   rd_data  = cam_stat_i[215:208];
            // 0x91: frames per scan (opcode 4), from the status snapshot's top byte
            8'h91:   rd_data  = {2'b0, cam_stat_i[221:216]};
            default: begin rd_data = 8'h00; rd_def = 1'b0; end
        endcase
    end

    // checksum helpers (8-bit wraparound)
    wire [7:0] w_sum  = OP_W  + addr + dbyte + rx_data; // == 0 -> good write CK
    wire [7:0] r_sum  = OP_R  + addr + rx_data;         // == 0 -> good read CK
    wire [7:0] u_sum  = sum8  + rx_data;                // == 0 -> good upload CK
    wire [7:0] rt_sum = OP_LR + dbyte + rx_data;        // == 0 -> good read-table request CK
    wire [7:0] rd_ck = (8'h00 - addr - rd_data);        // -(addr+data) mod 256
    wire [7:0] nd_ck = (8'h00 - ACK_N - addr);          // -('N'+addr): undefined read

    // Camera commit checks, on the value each commit would apply (dbyte is the top byte).
    wire [15:0] expo_new = {dbyte, expo_lo_s};
    wire [23:0] trig_new = {dbyte, trig_lo_s};
    // Genlocked: the vsync period governs and no register write can change it, so the
    // max exposure published by usb_link is authoritative. Free-running: the trigger
    // period governs, checked LIVE here.
    wire [24:0] expo_need = {2'b0, expo_ticks(expo_new)}  + {1'b0, RESERVE_TICKS};
    wire [24:0] live_need = {2'b0, expo_ticks(live_expo)} + {1'b0, RESERVE_TICKS};
    wire expo_ok = live_gl ? (maxexp_i[23] && (expo_new <= maxexp_i[15:0]))
                           : (expo_need <= {1'b0, live_trig});
    wire trig_ok = (trig_new > 24'd1000) && (live_gl || (live_need <= {1'b0, trig_new}));
    wire nfr_ok  = (dbyte[7:6] == 2'b00) && (dbyte[5:0] != 6'd0);

    integer i;
    always @(posedge clk) begin
        if (rst) begin
            state <= S_SYNC; tx_send <= 1'b0; sli_ctrl <= 8'h00;
            rx_idle <= 0; rx_timeout <= 1'b0;
            corr_ld <= 1'b0; lut_ld <= 1'b0; lutv_ld <= 1'b0;
            mode_force <= 8'h00;       // force_en=0 -> EDID pick is in charge
            link_drop_host <= 1'b0; link_drop_proj <= 1'b0;
            cam_sim <= 8'h00;
            link_active <= 1'b0; link_secs <= 6'd0; link_presc <= 26'd0; link_tgt <= 2'd0;
            resp_len <= 2'd0; resp_idx <= 2'd0;
            rb_active <= 1'b0; rb_ph <= 2'd0; rd_idx <= 12'd0;
            // camera: reset_n = cam_gpio[7] = 0 -> the sensor stays HELD IN RESET
            // until the host deliberately releases it.
            cam_spi_addr <= 9'd0; cam_spi_rw <= 1'b0; cam_spi_wdata <= 16'd0;
            cam_spi_start <= 1'b0; cam_gpio <= 8'h00;
            cam_rdata_l <= 16'd0; cam_done_l <= 1'b0;
            cam_boot_go <= 1'b0;
            cam_cmd_word <= 32'd0; cam_cmd_valid <= 1'b0;
            expo_lo_s <= 8'd0; trig_lo_s <= 16'd0; gl_dly_s <= 24'd0; idle_ms_s <= 16'd0;
        end else begin
            tx_send       <= 1'b0;                      // default: no TX strobe
            cam_spi_start <= 1'b0;                      // default: no SPI strobe
            cam_cmd_valid <= 1'b0;                      // default: no camera command

            // Inter-byte watchdog. Runs only while a frame is part-received.
            rx_timeout <= 1'b0;
            // rb_active/resp_len MUST hold it off: during a table READBACK the board
            // is transmitting and the host is correctly silent, so without this the
            // watchdog counts down against OUR OWN REPLY and aborts it. 50 ms at
            // 115200 baud is 576 bytes, so corr (256 B, 22 ms) survived while lut
            // (720 B) and lutv (1280 B) died -- test_silicon reported "first diff
            // @575" against a predicted cutoff of 576. Regression from 4e670bd
            // (2026-08-21); the recorded 15/15 predates it. The watchdog's real job --
            // aborting a stalled UPLOAD -- is unaffected, because rb_active is 0 then.
            if (state == S_SYNC || rx_valid || rb_active || resp_len != 2'd0) begin
                rx_idle <= 0;
            end else if (rx_idle == RX_IDLE_TICKS[$clog2(RX_IDLE_TICKS+1)-1:0]) begin
                rx_timeout <= 1'b1;                     // one-cycle abort pulse
                rx_idle    <= 0;
            end else begin
                rx_idle <= rx_idle + 1'b1;
            end
            cam_boot_go   <= 1'b0;                      // default: no boot strobe

            // Capture the SPI result whenever it lands, regardless of FSM state.
            // Placed BEFORE the case so that a GO arriving in the same cycle wins and
            // clears `done` (last non-blocking assignment takes effect).
            if (cam_spi_done) begin
                cam_rdata_l <= cam_spi_rdata;
                cam_done_l  <= 1'b1;
            end

            // ---- LINKCTL self-timer: hold the commanded disconnect(s) for link_secs
            // half-seconds, then release. Placed BEFORE the case so a fresh 0x15 write
            // (which re-arms link_active/secs/presc/tgt) overrides this same cycle.
            if (link_active) begin
                if (link_presc >= HALF_SEC-1) begin
                    link_presc <= 26'd0;
                    if (link_secs <= 6'd1) link_active <= 1'b0;
                    else                   link_secs   <= link_secs - 6'd1;
                end else link_presc <= link_presc + 26'd1;
            end
            link_drop_host <= link_active & link_tgt[0];
            link_drop_proj <= link_active & link_tgt[1];

            case (state)
                // ---- frame sync + opcode dispatch -------------------------
                S_SYNC: if (rx_valid && rx_data == SYNC) state <= S_OP;

                S_OP: if (rx_valid) begin
                    case (rx_data)
                        OP_W:  state <= S_WADDR;
                        OP_R:  state <= S_RADDR;
                        OP_L:  state <= S_UTGT;
                        OP_LR: state <= S_RTGT;
                        SYNC:    state <= S_OP;          // re-sync on a fresh A5
                        default: state <= S_SYNC;
                    endcase
                end

                // ---- write: A5 57 ADDR DATA CK ----------------------------
                S_WADDR: if (rx_valid) begin addr  <= rx_data; state <= S_WDATA; end
                S_WDATA: if (rx_valid) begin dbyte <= rx_data; state <= S_WCK;   end
                S_WCK:   if (rx_valid) begin
                    if (w_sum != 8'h00) begin            // bad checksum
                        resp[0] <= ACK_E; resp_len <= 2'd1;
                    end else if (addr == 8'h13) begin    // SLI control / overrides
                        sli_ctrl <= dbyte; resp[0] <= ACK_K; resp_len <= 2'd1;
                    end else if (addr == 8'h14) begin    // MODEFORCE (bring-up / test)
                        mode_force <= dbyte; resp[0] <= ACK_K; resp_len <= 2'd1;
                    end else if (addr == 8'h16) begin    // CAMSIM: host-driven rdy
                        cam_sim <= dbyte; resp[0] <= ACK_K; resp_len <= 2'd1;
                    end else if (addr == 8'h15) begin    // LINKCTL: self-timed disconnect
                        link_tgt    <= dbyte[1:0];
                        link_secs   <= dbyte[7:2];
                        link_presc  <= 26'd0;
                        link_active <= (dbyte[7:2] != 6'd0) && (dbyte[1:0] != 2'd0);
                        resp[0] <= ACK_K; resp_len <= 2'd1;
                    // ---- PYTHON 1300 SPI mailbox ----
                    end else if (addr == 8'h30) begin    // sensor addr[7:0]
                        cam_spi_addr[7:0] <= dbyte;      resp[0] <= ACK_K; resp_len <= 2'd1;
                    end else if (addr == 8'h31) begin    // {rw, -, addr[8]}
                        cam_spi_rw    <= dbyte[7];
                        cam_spi_addr[8] <= dbyte[0];     resp[0] <= ACK_K; resp_len <= 2'd1;
                    end else if (addr == 8'h32) begin    // wdata[7:0]
                        cam_spi_wdata[7:0]  <= dbyte;    resp[0] <= ACK_K; resp_len <= 2'd1;
                    end else if (addr == 8'h33) begin    // wdata[15:8]
                        cam_spi_wdata[15:8] <= dbyte;    resp[0] <= ACK_K; resp_len <= 2'd1;
                    end else if (addr == 8'h34) begin    // GO (any value fires it)
                        // Drop the GO if a transaction is still running, rather than
                        // silently corrupting the operands mid-flight. The host polls
                        // busy anyway; 'N' tells it plainly that the GO did not take.
                        if (cam_spi_busy) begin
                            resp[0] <= ACK_N; resp_len <= 2'd1;
                        end else begin
                            cam_spi_start <= 1'b1;
                            cam_done_l    <= 1'b0;       // arm: cleared until this one lands
                            resp[0] <= ACK_K; resp_len <= 2'd1;
                        end
                    end else if (addr == 8'h37) begin    // {reset_n, -, trigger[2:0]}
                        cam_gpio <= dbyte;               resp[0] <= ACK_K; resp_len <= 2'd1;
                    end else if (addr == 8'h39) begin    // boot sequencer GO (any value)
                        // Drop the GO if a boot is already running (busy = cam_boot_stat[2]),
                        // same policy as the SPI GO at 0x34: 'N' tells the host it did not take.
                        if (cam_boot_stat[2]) begin
                            resp[0] <= ACK_N; resp_len <= 2'd1;
                        end else begin
                            cam_boot_go <= 1'b1;
                            // Release reset (cam_gpio[7]) as part of issuing boot. The sequencer
                            // drives reset itself while busy; this makes ownership hand BACK to a
                            // released state when it finishes, so a just-booted sensor is not yanked
                            // into reset if the host had not already set reg 0x37 bit 7. The host
                            // still controls reset afterward via 0x37.
                            cam_gpio[7] <= 1'b1;
                            resp[0] <= ACK_K; resp_len <= 2'd1;
                        end
                    // ---- camera settings: stage low bytes, commit on the top byte ----
                    end else if (addr == 8'h40) begin    // exposure lo (staged)
                        expo_lo_s <= dbyte;              resp[0] <= ACK_K; resp_len <= 2'd1;
                    end else if (addr == 8'h41) begin    // exposure hi -> COMMIT
                        if (expo_ok) begin
                            cam_cmd_word  <= {4'd1, 12'd0, expo_new};
                            cam_cmd_valid <= 1'b1;
                            resp[0] <= ACK_K;
                        end else resp[0] <= ACK_N;       // would wedge the sensor
                        resp_len <= 2'd1;
                    end else if (addr == 8'h5A) begin    // genlock delay (staged)
                        gl_dly_s[7:0]   <= dbyte;        resp[0] <= ACK_K; resp_len <= 2'd1;
                    end else if (addr == 8'h5B) begin
                        gl_dly_s[15:8]  <= dbyte;        resp[0] <= ACK_K; resp_len <= 2'd1;
                    end else if (addr == 8'h5C) begin
                        gl_dly_s[23:16] <= dbyte;        resp[0] <= ACK_K; resp_len <= 2'd1;
                    end else if (addr == 8'h5D) begin    // genlock enable -> COMMIT
                        cam_cmd_word  <= {4'd7, dbyte[0], 3'd0, gl_dly_s};
                        cam_cmd_valid <= 1'b1;
                        resp[0] <= ACK_K; resp_len <= 2'd1;
                    end else if (addr == 8'h8E) begin    // trigger period lo (staged)
                        trig_lo_s[7:0]  <= dbyte;        resp[0] <= ACK_K; resp_len <= 2'd1;
                    end else if (addr == 8'h8F) begin    // trigger period mid (staged)
                        trig_lo_s[15:8] <= dbyte;        resp[0] <= ACK_K; resp_len <= 2'd1;
                    end else if (addr == 8'h90) begin    // trigger period hi -> COMMIT
                        if (trig_ok) begin
                            cam_cmd_word  <= {4'd2, 4'd0, trig_new};
                            cam_cmd_valid <= 1'b1;
                            resp[0] <= ACK_K;
                        end else resp[0] <= ACK_N;
                        resp_len <= 2'd1;
                    end else if (addr == 8'h91) begin    // frames per scan -> COMMIT
                        if (nfr_ok) begin
                            cam_cmd_word  <= {4'd4, 22'd0, dbyte[5:0]};
                            cam_cmd_valid <= 1'b1;
                            resp[0] <= ACK_K;
                        end else resp[0] <= ACK_N;       // 0 never terminates a scan
                        resp_len <= 2'd1;
                    // ---- camera commands ----
                    end else if (addr == 8'h17) begin    // CAMCMD: bit0 re-arm
                        if (dbyte[0]) begin
                            cam_cmd_word  <= {4'd3, 28'd0};
                            cam_cmd_valid <= 1'b1;
                        end
                        resp[0] <= ACK_K; resp_len <= 2'd1;
                    end else if (addr == 8'h18) begin    // idle ms lo (staged)
                        idle_ms_s[7:0]  <= dbyte;        resp[0] <= ACK_K; resp_len <= 2'd1;
                    end else if (addr == 8'h19) begin    // idle ms hi (staged)
                        idle_ms_s[15:8] <= dbyte;        resp[0] <= ACK_K; resp_len <= 2'd1;
                    end else if (addr == 8'h1A) begin    // CAMIDLE -> COMMIT
                        cam_cmd_word  <= {4'd6, dbyte[0], 11'd0, idle_ms_s};
                        cam_cmd_valid <= 1'b1;
                        resp[0] <= ACK_K; resp_len <= 2'd1;
                    end else begin                       // RO / undefined
                        resp[0] <= ACK_N; resp_len <= 2'd1;
                    end
                    resp_idx <= 2'd0; state <= S_RESP;
                end

                // ---- read: A5 52 ADDR CK ; reply ADDR DATA CK2 ------------
                S_RADDR: if (rx_valid) begin addr <= rx_data; state <= S_RCK; end
                S_RCK:   if (rx_valid) begin
                    if (r_sum != 8'h00) begin            // bad request checksum
                        resp[0] <= ACK_E; resp_len <= 2'd1;
                    end else if (!rd_def) begin          // no such register: 'N' ADDR CK3
                        resp[0] <= ACK_N; resp[1] <= addr; resp[2] <= nd_ck;
                        resp_len <= 2'd3;
                    end else begin
                        resp[0] <= addr; resp[1] <= rd_data; resp[2] <= rd_ck;
                        resp_len <= 2'd3;
                    end
                    resp_idx <= 2'd0; state <= S_RESP;
                end

                // ---- upload: A5 5B TGT D[0..N-1] CK ----------------------
                S_UTGT: if (rx_valid) begin
                    sum8 <= rx_data;                     // CK base = TARGET
                    cnt  <= 12'd0;
                    case (rx_data)
                        TGT_LUT:  begin tgt <= 3'd0; len <= 12'd720;  state <= S_UDATA; end
                        TGT_LUTV: begin tgt <= 3'd1; len <= 12'd1280; state <= S_UDATA; end
                        TGT_CORR: begin tgt <= 3'd2; len <= 12'd256;  state <= S_UDATA; end
                        default:  begin                  // unknown target -> 'E' (incl. read-only cam_line)
                            resp[0] <= ACK_E; resp_len <= 2'd1; resp_idx <= 2'd0;
                            state <= S_RESP;
                        end
                    endcase
                end
                S_UDATA: if (rx_valid) begin
                    case (tgt)
                        3'd0: lut [cnt[9:0]]  <= rx_data;
                        3'd1: lutv[cnt[10:0]] <= rx_data;
                        3'd2: corr[cnt[7:0]]  <= rx_data;
                    endcase
                    sum8 <= sum8 + rx_data;
                    if (cnt == len - 12'd1) state <= S_UCK;
                    else cnt <= cnt + 12'd1;
                end
                S_UCK: if (rx_valid) begin
                    if (u_sum == 8'h00) begin            // good -> commit (set loaded)
                        case (tgt)
                            3'd0: lut_ld  <= 1'b1;
                            3'd1: lutv_ld <= 1'b1;
                            3'd2: corr_ld <= 1'b1;
                        endcase
                        resp[0] <= ACK_K;
                    end else begin
                        resp[0] <= ACK_E;                // bad checksum
                    end
                    resp_len <= 2'd1; resp_idx <= 2'd0; state <= S_RESP;
                end

                // ---- read-table: A5 72 TGT CK ; reply TGT D[0..N-1] CK2 ---
                S_RTGT: if (rx_valid) begin
                    dbyte <= rx_data;                    // raw target (checksum + prologue)
                    case (rx_data)
                        TGT_LUT:      begin tgt <= 3'd0; len <= 12'd720;  end
                        TGT_LUTV:     begin tgt <= 3'd1; len <= 12'd1280; end
                        TGT_CORR:     begin tgt <= 3'd2; len <= 12'd256;  end
                        TGT_EDID:     begin tgt <= 3'd3; len <= 12'd256;  end   // read-only
                        TGT_CAM_LINE: begin tgt <= 3'd4; len <= CAM_LINE_LEN[11:0]; end  // read-only
                        TGT_EDID_SRV: begin tgt <= 3'd5; len <= 12'd256;  end   // read-only
                        default:      begin tgt <= 3'd0; len <= 12'd0;    end   // unknown -> rejected
                    endcase
                    state <= S_RTCK;
                end
                S_RTCK: if (rx_valid) begin
                    if ((rt_sum != 8'h00) || (len == 12'd0)) begin   // bad CK or unknown target
                        resp[0] <= ACK_E; resp_len <= 2'd1; resp_idx <= 2'd0;
                        state <= S_RESP;
                    end else begin
                        sum8 <= dbyte;                   // checksum base = target
                        rd_idx <= 12'd0; rb_active <= 1'b1; rb_ph <= 2'd0;
                        state <= S_RTAB;
                    end
                end
                S_RTAB: if (!tx_busy && !tx_send) begin
                    case (rb_ph)
                        2'd0: begin                      // prologue: echo target
                            tx_data <= dbyte; tx_send <= 1'b1;
                            rd_idx <= 12'd0; rb_ph <= 2'd1;
                        end
                        2'd1: begin                      // stream data bytes from RAM
                            tx_data <= rb_dout; tx_send <= 1'b1;
                            sum8 <= sum8 + rb_dout;
                            if (rd_idx == len - 12'd1) rb_ph <= 2'd2;
                            else rd_idx <= rd_idx + 12'd1;
                        end
                        default: begin                   // epilogue: checksum byte, done
                            tx_data <= (8'h00 - sum8); tx_send <= 1'b1;
                            rb_active <= 1'b0; state <= S_SYNC;
                        end
                    endcase
                end

                // ---- response: push resp[0..len-1] to the shared uart_tx --
                S_RESP: begin
                    if (!tx_busy && !tx_send) begin
                        tx_data <= resp[resp_idx];
                        tx_send <= 1'b1;
                        if (resp_idx == resp_len - 2'd1) state <= S_SYNC;
                        else resp_idx <= resp_idx + 2'd1;
                    end
                end

                default: state <= S_SYNC;
            endcase

            // ABORT LAST, AFTER the case, so it overrides whatever the state
            // machine decided this cycle. Placed earlier, a mid-frame transition
            // would win the race and the frame would stay stuck.
            //
            // Deliberately SILENT: the sender is gone, so there is nobody to send
            // an error byte to, and emitting one would only desynchronise the next
            // host that connects. Dropping the partial frame and resyncing on the
            // next SYNC is the whole cure.
            if (rx_timeout) begin
                state     <= S_SYNC;
                resp_len  <= 2'd0;
                resp_idx  <= 2'd0;
                rb_active <= 1'b0;
            end
        end
    end
endmodule
