drhalftone/AuV2-SLI/sources_1/imports/RTL/drp_recfg.v

`timescale 1ps/1ps   // MUST match XAPP888 mmcm_drp.v: TCQ=100 is a 100 ps clock-to-Q.
                     // Under 1ns/1ps it would be 100 ns (10 clk100 periods) and the
                     // FSM/DRP timing falls apart in sim (MMCM never re-locks).
//==============================================================================
// drp_recfg - 13-mode MMCM DRP reconfiguration controller (Phase D2).
//
//   Generalises the XAPP888 mmcm_drp 2-state controller to the full curated mode
//   table. The read-modify-write FSM is the proven XAPP888 one verbatim; the only
//   change is that the 23-register write sequence is driven by ONE combinational
//   ROM whose values come from the selected mode's M/D/O (looked up by mode_idx and
//   turned into DRP words by the same mmcm_drp_func.h functions, constant-folded
//   per mode). CLKOUT0=CLKOUT1=pixel(=x1), CLKOUT2=x5(=5*pixel); CLKOUT3..6 unused.
//
//   Per-mode integer M(mult) / D(divclk) / O0(pixel divide) / O2(x5 divide), in the
//   SAME index order as mode_table.vh. NOTE: index != priority (mode_select walks an
//   explicit PRIO[] list); 12 is the failsafe. drp_recfg is 14-mode as of idx13.
//     idx mode          M   D  O0  O2     pixel
//      0  800x600@120   11  1  15   3   73.33 MHz
//      1  640x480@120   55  7  15   3   52.38
//      2  1024x768@75   59  5  15   3   78.67
//      3  800x600@75    52  7  15   3   49.52
//      4  640x480@75    63  5  40   8   31.50   <- exact (see note below)
//      5  1024x768@70   15  2  10   2   75.00
//      6  800x600@72    10  1  20   4   50.00
//      7  640x480@72    63  5  40   8   31.50   <- exact (see note below)
//      8  1280x720@60   52  7  10   2   74.29
//      9  1280x800@60   32  3  15   3   71.11
//     10  1024x768@60   13  2  10   2   65.00
//     11  800x600@60    12  1  30   6   40.00   <- was 6/1/15/3 (VCO 600 = the
//                                                  rated MINIMUM; display rejected it)
//     12  640x480@60    34  3  45   9   25.19  (failsafe)
//     13  1280x1024@60  54  5  10   2  108.00   <- FASTEST (x5=540MHz; MMCM power-up = this)
//
//   Pixel clock accuracy. Reachable set is 20*M/(O2*D) with integer M/D/O and
//   O0 = 5*O2 (the serializer needs an exactly-5x clock), so most targets are only
//   approachable, not hittable. Pick the HIGHEST VCO among near-exact candidates:
//   MMCM jitter falls as VCO rises (UG472: run the VCO as fast as possible).
//
//   idx4/idx7 (31.5 MHz) used to be M=11 D=1 O0=35 -> 31.43 MHz (-0.227%) at
//   VCO 1100. M=63 D=5 O0=40 is EXACT and runs VCO at 1260 -- more accurate AND
//   lower jitter, so it is a strict win with no trade-off.
//
//   idx2 (78.75 MHz) is DELIBERATELY LEFT INEXACT. The only exact solution is
//   M=63 D=8 O0=10, which drops VCO from 1180 -> 787.5 MHz (-33%) and so raises
//   jitter, on the fastest link we drive (x5 = 394 MHz, where the OSERDES
//   parallel-load margin already blacked the output once -- see clk_selector.v).
//   M=59 D=5 (78.667 MHz, -0.106%) keeps the VCO high and is the right trade:
//   nothing observes the 0.1% (the FPGA clocks both the pattern and the camera
//   trigger, so they stay coherent regardless). DO NOT "fix" idx2 to 78.75.
//
//   Reconfig: present MODE_IDX, pulse SEN for 1 SCLK; SRDY strobes when re-locked.
//==============================================================================
module drp_recfg (
    input             SCLK,
    input             RST,
    input      [3:0]  MODE_IDX,
    input             SEN,
    output reg        SRDY,
    // to/from MMCME2_ADV
    input      [15:0] DO,
    input             DRDY,
    input             LOCKED,
    output reg        DWE,
    output reg        DEN,
    output reg [6:0]  DADDR,
    output reg [15:0] DI,
    output            DCLK,
    output reg        RST_MMCM
);
    localparam TCQ = 100;
    assign DCLK = SCLK;

    `include "mmcm_drp_func.h"

    // ---- FSM state encodings ----
    localparam RESTART=4'h1, WAIT_LOCK=4'h2, WAIT_SEN=4'h3, ADDRESS=4'h4,
               WAIT_A_DRDY=4'h5, BITMASK=4'h6, BITSET=4'h7, WRITE=4'h8, WAIT_DRDY=4'h9;
    localparam STATE_COUNT_CONST = 23;
    localparam [37:0] CNT1 = mmcm_count_calc(8'd1, 0, 50000);   // unused CLKOUT3..6 = /1

    // ---- declarations (all module-level state up front) ----
    reg [3:0]  sel = 4'd13;                // selected mode; power-up = FASTEST (idx13, 108 MHz)
                                           // must match drp_clkgen13's MMCME2_ADV power-up params
    reg [37:0] selCLKOUT0, selCLKOUT2, selCLKFB, selDIVCLK;
    reg [39:0] selLOCK;
    reg [9:0]  selFILT;
    reg [38:0] rom_comb;
    reg [5:0]  rom_addr, next_rom_addr;
    reg [38:0] rom_do;
    reg [3:0]  current_state = RESTART, next_state = RESTART;
    reg [4:0]  state_count = STATE_COUNT_CONST, next_state_count = STATE_COUNT_CONST;
    reg        next_srdy, next_dwe, next_den, next_rst_mmcm;
    reg [6:0]  next_daddr;
    reg [15:0] next_di;
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
